jabadiagm/MSXgoauld_x/fpga/Goauld_x.srcs/sources_1/ip/ila_0_1/synth/ila_0.v

// (c) Copyright 1995-2012 Xilinx, Inc. All rights reserved.
//
// This file contains confidential and proprietary information
// of Xilinx, Inc. and is protected under U.S. and
// international copyright and other intellectual property
// laws.
//
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
// CRITICAL APPLICATIONS
// Xilinx products are not designed or intended to be fail-
// safe, or for use in any application requiring fail-safe
// performance, such as life-support or safety devices or
// systems, Class III medical devices, nuclear facilities,
// applications related to the deployment of airbags, or any
// other applications that could lead to death, personal
// injury, or severe property or environmental damage
// (individually and collectively, "Critical
// Applications"). Customer assumes the sole risk and
// liability of any use of Xilinx products in Critical
// Applications, subject only to applicable laws and
// regulations governing limitations on product liability.
//
// THIS COPYRIGHT NOTICE AND DISCLAIMER MUST BE RETAINED AS
// PART OF THIS FILE AT ALL TIMES.
//
// DO NOT MODIFY THIS FILE.
(* DowngradeIPIdentifiedWarnings="yes" *)
(* X_CORE_INFO = "ila,Vivado 2019.1" *)
(* CHECK_LICENSE_TYPE = "ila_0,ila,{}" *)
(* CORE_GENERATION_INFO = "ila_0,ila,{x_ipProduct=Vivado 2019.1,x_ipVendor=xilinx.com,x_ipLibrary=ip,x_ipName=ila,x_ipVersion=6.2,x_ipLanguage=VERILOG,C_XLNX_HW_PROBE_INFO=DEFAULT,C_XDEVICEFAMILY=artix7,C_CORE_TYPE=1,C_CORE_INFO1=0,C_CORE_INFO2=0,C_CAPTURE_TYPE=0,C_MU_TYPE=0,C_TC_TYPE=0,C_NUM_OF_PROBES=28,C_DATA_DEPTH=2048,C_MAJOR_VERSION=2019,C_MINOR_VERSION=1,C_BUILD_REVISION=0,C_CORE_MAJOR_VER=6,C_CORE_MINOR_VER=2,C_XSDB_SLAVE_TYPE=17,C_NEXT_SLAVE=0,C_CSE_DRV_VER=2,C_USE_TEST_REG=1,C_PIPE_IFACE=1,C_RAM_STYLE=SUBCORE,C_TRIGOUT_EN=0,C_TRIGIN_EN=0,C_ADV_TRIGGER=0,C_EN_DDR_ILA=0,C_DDR_CLK_GEN=0,C_CLK_FREQ=200,C_CLK_PERIOD=5.0,C_CLKFBOUT_MULT_F=10,C_DIVCLK_DIVIDE=3,C_CLKOUT0_DIVIDE_F=10,C_EN_STRG_QUAL=0,C_INPUT_PIPE_STAGES=0,ALL_PROBE_SAME_MU=TRUE,ALL_PROBE_SAME_MU_CNT=1,C_EN_TIME_TAG=0,C_TIME_TAG_WIDTH=32,C_ILA_CLK_FREQ=2000000,C_PROBE0_WIDTH=25,C_PROBE1_WIDTH=24,C_PROBE2_WIDTH=8,C_PROBE3_WIDTH=1,C_PROBE4_WIDTH=1,C_PROBE5_WIDTH=4,C_PROBE6_WIDTH=25,C_PROBE7_WIDTH=1,C_PROBE8_WIDTH=1,C_PROBE9_WIDTH=8,C_PROBE10_WIDTH=16,C_PROBE11_WIDTH=1,C_PROBE12_WIDTH=1,C_PROBE13_WIDTH=4,C_PROBE14_WIDTH=8,C_PROBE15_WIDTH=1,C_PROBE16_WIDTH=1,C_PROBE17_WIDTH=1,C_PROBE18_WIDTH=1,C_PROBE19_WIDTH=1,C_PROBE20_WIDTH=1,C_PROBE21_WIDTH=1,C_PROBE22_WIDTH=1,C_PROBE23_WIDTH=1,C_PROBE24_WIDTH=16,C_PROBE25_WIDTH=8,C_PROBE26_WIDTH=1,C_PROBE27_WIDTH=1,C_PROBE28_WIDTH=1,C_PROBE29_WIDTH=1,C_PROBE30_WIDTH=1,C_PROBE31_WIDTH=1,C_PROBE32_WIDTH=1,C_PROBE33_WIDTH=1,C_PROBE34_WIDTH=1,C_PROBE35_WIDTH=1,C_PROBE36_WIDTH=1,C_PROBE37_WIDTH=1,C_PROBE38_WIDTH=1,C_PROBE39_WIDTH=1,C_PROBE40_WIDTH=1,C_PROBE41_WIDTH=1,C_PROBE42_WIDTH=1,C_PROBE43_WIDTH=1,C_PROBE44_WIDTH=1,C_PROBE45_WIDTH=1,C_PROBE46_WIDTH=1,C_PROBE47_WIDTH=1,C_PROBE48_WIDTH=1,C_PROBE49_WIDTH=1,C_PROBE50_WIDTH=1,C_PROBE51_WIDTH=1,C_PROBE52_WIDTH=1,C_PROBE53_WIDTH=1,\
C_PROBE54_WIDTH=1,C_PROBE55_WIDTH=1,C_PROBE56_WIDTH=1,C_PROBE57_WIDTH=1,C_PROBE58_WIDTH=1,C_PROBE59_WIDTH=1,C_PROBE60_WIDTH=1,C_PROBE61_WIDTH=1,C_PROBE62_WIDTH=1,C_PROBE63_WIDTH=1,C_PROBE64_WIDTH=1,C_PROBE65_WIDTH=1,C_PROBE66_WIDTH=1,C_PROBE67_WIDTH=1,C_PROBE68_WIDTH=1,C_PROBE69_WIDTH=1,C_PROBE70_WIDTH=1,C_PROBE71_WIDTH=1,C_PROBE72_WIDTH=1,C_PROBE73_WIDTH=1,C_PROBE74_WIDTH=1,C_PROBE75_WIDTH=1,C_PROBE76_WIDTH=1,C_PROBE77_WIDTH=1,C_PROBE78_WIDTH=1,C_PROBE79_WIDTH=1,C_PROBE80_WIDTH=1,C_PROBE81_WIDTH=1,C_PROBE82_WIDTH=1,C_PROBE83_WIDTH=1,C_PROBE84_WIDTH=1,C_PROBE85_WIDTH=1,C_PROBE86_WIDTH=1,C_PROBE87_WIDTH=1,C_PROBE88_WIDTH=1,C_PROBE89_WIDTH=1,C_PROBE90_WIDTH=1,C_PROBE91_WIDTH=1,C_PROBE92_WIDTH=1,C_PROBE93_WIDTH=1,C_PROBE94_WIDTH=1,C_PROBE95_WIDTH=1,C_PROBE96_WIDTH=1,C_PROBE97_WIDTH=1,C_PROBE98_WIDTH=1,C_PROBE99_WIDTH=1,C_PROBE100_WIDTH=1,C_PROBE101_WIDTH=1,C_PROBE102_WIDTH=1,C_PROBE103_WIDTH=1,C_PROBE104_WIDTH=1,C_PROBE105_WIDTH=1,C_PROBE106_WIDTH=1,C_PROBE107_WIDTH=1,C_PROBE108_WIDTH=1,C_PROBE109_WIDTH=1,C_PROBE110_WIDTH=1,C_PROBE111_WIDTH=1,C_PROBE112_WIDTH=1,C_PROBE113_WIDTH=1,C_PROBE114_WIDTH=1,C_PROBE115_WIDTH=1,C_PROBE116_WIDTH=1,C_PROBE117_WIDTH=1,C_PROBE118_WIDTH=1,C_PROBE119_WIDTH=1,C_PROBE120_WIDTH=1,C_PROBE121_WIDTH=1,C_PROBE122_WIDTH=1,C_PROBE123_WIDTH=1,C_PROBE124_WIDTH=1,C_PROBE125_WIDTH=1,C_PROBE126_WIDTH=1,C_PROBE127_WIDTH=1,C_PROBE128_WIDTH=1,C_PROBE129_WIDTH=1,C_PROBE130_WIDTH=1,C_PROBE131_WIDTH=1,C_PROBE132_WIDTH=1,C_PROBE133_WIDTH=1,C_PROBE134_WIDTH=1,C_PROBE135_WIDTH=1,C_PROBE136_WIDTH=1,C_PROBE137_WIDTH=1,C_PROBE138_WIDTH=1,C_PROBE139_WIDTH=1,C_PROBE140_WIDTH=1,C_PROBE141_WIDTH=1,C_PROBE142_WIDTH=1,C_PROBE143_WIDTH=1,C_PROBE144_WIDTH=1,C_PROBE145_WIDTH=1,C_PROBE146_WIDTH=1,C_PROBE147_WIDTH=1,C_PROBE148_WIDTH=1,C_PROBE149_WIDTH=1,C_PROBE150_WIDTH=1,C_PROBE151_WIDTH=1,C_PROBE152_WIDTH=1,C_PROBE153_WIDTH=1,\
C_PROBE154_WIDTH=1,C_PROBE155_WIDTH=1,C_PROBE156_WIDTH=1,C_PROBE157_WIDTH=1,C_PROBE158_WIDTH=1,C_PROBE159_WIDTH=1,C_PROBE160_WIDTH=1,C_PROBE161_WIDTH=1,C_PROBE162_WIDTH=1,C_PROBE163_WIDTH=1,C_PROBE164_WIDTH=1,C_PROBE165_WIDTH=1,C_PROBE166_WIDTH=1,C_PROBE167_WIDTH=1,C_PROBE168_WIDTH=1,C_PROBE169_WIDTH=1,C_PROBE170_WIDTH=1,C_PROBE171_WIDTH=1,C_PROBE172_WIDTH=1,C_PROBE173_WIDTH=1,C_PROBE174_WIDTH=1,C_PROBE175_WIDTH=1,C_PROBE176_WIDTH=1,C_PROBE177_WIDTH=1,C_PROBE178_WIDTH=1,C_PROBE179_WIDTH=1,C_PROBE180_WIDTH=1,C_PROBE181_WIDTH=1,C_PROBE182_WIDTH=1,C_PROBE183_WIDTH=1,C_PROBE184_WIDTH=1,C_PROBE185_WIDTH=1,C_PROBE186_WIDTH=1,C_PROBE187_WIDTH=1,C_PROBE188_WIDTH=1,C_PROBE189_WIDTH=1,C_PROBE190_WIDTH=1,C_PROBE191_WIDTH=1,C_PROBE192_WIDTH=1,C_PROBE193_WIDTH=1,C_PROBE194_WIDTH=1,C_PROBE195_WIDTH=1,C_PROBE196_WIDTH=1,C_PROBE197_WIDTH=1,C_PROBE198_WIDTH=1,C_PROBE199_WIDTH=1,C_PROBE200_WIDTH=1,C_PROBE201_WIDTH=1,C_PROBE202_WIDTH=1,C_PROBE203_WIDTH=1,C_PROBE204_WIDTH=1,C_PROBE205_WIDTH=1,C_PROBE206_WIDTH=1,C_PROBE207_WIDTH=1,C_PROBE208_WIDTH=1,C_PROBE209_WIDTH=1,C_PROBE210_WIDTH=1,C_PROBE211_WIDTH=1,C_PROBE212_WIDTH=1,C_PROBE213_WIDTH=1,C_PROBE214_WIDTH=1,C_PROBE215_WIDTH=1,C_PROBE216_WIDTH=1,C_PROBE217_WIDTH=1,C_PROBE218_WIDTH=1,C_PROBE219_WIDTH=1,C_PROBE220_WIDTH=1,C_PROBE221_WIDTH=1,C_PROBE222_WIDTH=1,C_PROBE223_WIDTH=1,C_PROBE224_WIDTH=1,C_PROBE225_WIDTH=1,C_PROBE226_WIDTH=1,C_PROBE227_WIDTH=1,C_PROBE228_WIDTH=1,C_PROBE229_WIDTH=1,C_PROBE230_WIDTH=1,C_PROBE231_WIDTH=1,C_PROBE232_WIDTH=1,C_PROBE233_WIDTH=1,C_PROBE234_WIDTH=1,C_PROBE235_WIDTH=1,C_PROBE236_WIDTH=1,C_PROBE237_WIDTH=1,C_PROBE238_WIDTH=1,C_PROBE239_WIDTH=1,C_PROBE240_WIDTH=1,C_PROBE241_WIDTH=1,C_PROBE242_WIDTH=1,C_PROBE243_WIDTH=1,C_PROBE244_WIDTH=1,C_PROBE245_WIDTH=1,C_PROBE246_WIDTH=1,C_PROBE247_WIDTH=1,C_PROBE248_WIDTH=1,C_PROBE249_WIDTH=1,C_PROBE250_WIDTH=1,C_PROBE251_WIDTH=1,C_PROBE252_WIDTH=1,C_PROBE253_WIDTH=1,\
C_PROBE254_WIDTH=1,C_PROBE255_WIDTH=1,C_PROBE256_WIDTH=1,C_PROBE257_WIDTH=1,C_PROBE258_WIDTH=1,C_PROBE259_WIDTH=1,C_PROBE260_WIDTH=1,C_PROBE261_WIDTH=1,C_PROBE262_WIDTH=1,C_PROBE263_WIDTH=1,C_PROBE264_WIDTH=1,C_PROBE265_WIDTH=1,C_PROBE266_WIDTH=1,C_PROBE267_WIDTH=1,C_PROBE268_WIDTH=1,C_PROBE269_WIDTH=1,C_PROBE270_WIDTH=1,C_PROBE271_WIDTH=1,C_PROBE272_WIDTH=1,C_PROBE273_WIDTH=1,C_PROBE274_WIDTH=1,C_PROBE275_WIDTH=1,C_PROBE276_WIDTH=1,C_PROBE277_WIDTH=1,C_PROBE278_WIDTH=1,C_PROBE279_WIDTH=1,C_PROBE280_WIDTH=1,C_PROBE281_WIDTH=1,C_PROBE282_WIDTH=1,C_PROBE283_WIDTH=1,C_PROBE284_WIDTH=1,C_PROBE285_WIDTH=1,C_PROBE286_WIDTH=1,C_PROBE287_WIDTH=1,C_PROBE288_WIDTH=1,C_PROBE289_WIDTH=1,C_PROBE290_WIDTH=1,C_PROBE291_WIDTH=1,C_PROBE292_WIDTH=1,C_PROBE293_WIDTH=1,C_PROBE294_WIDTH=1,C_PROBE295_WIDTH=1,C_PROBE296_WIDTH=1,C_PROBE297_WIDTH=1,C_PROBE298_WIDTH=1,C_PROBE299_WIDTH=1,C_PROBE300_WIDTH=1,C_PROBE301_WIDTH=1,C_PROBE302_WIDTH=1,C_PROBE303_WIDTH=1,C_PROBE304_WIDTH=1,C_PROBE305_WIDTH=1,C_PROBE306_WIDTH=1,C_PROBE307_WIDTH=1,C_PROBE308_WIDTH=1,C_PROBE309_WIDTH=1,C_PROBE310_WIDTH=1,C_PROBE311_WIDTH=1,C_PROBE312_WIDTH=1,C_PROBE313_WIDTH=1,C_PROBE314_WIDTH=1,C_PROBE315_WIDTH=1,C_PROBE316_WIDTH=1,C_PROBE317_WIDTH=1,C_PROBE318_WIDTH=1,C_PROBE319_WIDTH=1,C_PROBE320_WIDTH=1,C_PROBE321_WIDTH=1,C_PROBE322_WIDTH=1,C_PROBE323_WIDTH=1,C_PROBE324_WIDTH=1,C_PROBE325_WIDTH=1,C_PROBE326_WIDTH=1,C_PROBE327_WIDTH=1,C_PROBE328_WIDTH=1,C_PROBE329_WIDTH=1,C_PROBE330_WIDTH=1,C_PROBE331_WIDTH=1,C_PROBE332_WIDTH=1,C_PROBE333_WIDTH=1,C_PROBE334_WIDTH=1,C_PROBE335_WIDTH=1,C_PROBE336_WIDTH=1,C_PROBE337_WIDTH=1,C_PROBE338_WIDTH=1,C_PROBE339_WIDTH=1,C_PROBE340_WIDTH=1,C_PROBE341_WIDTH=1,C_PROBE342_WIDTH=1,C_PROBE343_WIDTH=1,C_PROBE344_WIDTH=1,C_PROBE345_WIDTH=1,C_PROBE346_WIDTH=1,C_PROBE347_WIDTH=1,C_PROBE348_WIDTH=1,C_PROBE349_WIDTH=1,C_PROBE350_WIDTH=1,C_PROBE351_WIDTH=1,C_PROBE352_WIDTH=1,C_PROBE353_WIDTH=1,\
C_PROBE354_WIDTH=1,C_PROBE355_WIDTH=1,C_PROBE356_WIDTH=1,C_PROBE357_WIDTH=1,C_PROBE358_WIDTH=1,C_PROBE359_WIDTH=1,C_PROBE360_WIDTH=1,C_PROBE361_WIDTH=1,C_PROBE362_WIDTH=1,C_PROBE363_WIDTH=1,C_PROBE364_WIDTH=1,C_PROBE365_WIDTH=1,C_PROBE366_WIDTH=1,C_PROBE367_WIDTH=1,C_PROBE368_WIDTH=1,C_PROBE369_WIDTH=1,C_PROBE370_WIDTH=1,C_PROBE371_WIDTH=1,C_PROBE372_WIDTH=1,C_PROBE373_WIDTH=1,C_PROBE374_WIDTH=1,C_PROBE375_WIDTH=1,C_PROBE376_WIDTH=1,C_PROBE377_WIDTH=1,C_PROBE378_WIDTH=1,C_PROBE379_WIDTH=1,C_PROBE380_WIDTH=1,C_PROBE381_WIDTH=1,C_PROBE382_WIDTH=1,C_PROBE383_WIDTH=1,C_PROBE384_WIDTH=1,C_PROBE385_WIDTH=1,C_PROBE386_WIDTH=1,C_PROBE387_WIDTH=1,C_PROBE388_WIDTH=1,C_PROBE389_WIDTH=1,C_PROBE390_WIDTH=1,C_PROBE391_WIDTH=1,C_PROBE392_WIDTH=1,C_PROBE393_WIDTH=1,C_PROBE394_WIDTH=1,C_PROBE395_WIDTH=1,C_PROBE396_WIDTH=1,C_PROBE397_WIDTH=1,C_PROBE398_WIDTH=1,C_PROBE399_WIDTH=1,C_PROBE400_WIDTH=1,C_PROBE401_WIDTH=1,C_PROBE402_WIDTH=1,C_PROBE403_WIDTH=1,C_PROBE404_WIDTH=1,C_PROBE405_WIDTH=1,C_PROBE406_WIDTH=1,C_PROBE407_WIDTH=1,C_PROBE408_WIDTH=1,C_PROBE409_WIDTH=1,C_PROBE410_WIDTH=1,C_PROBE411_WIDTH=1,C_PROBE412_WIDTH=1,C_PROBE413_WIDTH=1,C_PROBE414_WIDTH=1,C_PROBE415_WIDTH=1,C_PROBE416_WIDTH=1,C_PROBE417_WIDTH=1,C_PROBE418_WIDTH=1,C_PROBE419_WIDTH=1,C_PROBE420_WIDTH=1,C_PROBE421_WIDTH=1,C_PROBE422_WIDTH=1,C_PROBE423_WIDTH=1,C_PROBE424_WIDTH=1,C_PROBE425_WIDTH=1,C_PROBE426_WIDTH=1,C_PROBE427_WIDTH=1,C_PROBE428_WIDTH=1,C_PROBE429_WIDTH=1,C_PROBE430_WIDTH=1,C_PROBE431_WIDTH=1,C_PROBE432_WIDTH=1,C_PROBE433_WIDTH=1,C_PROBE434_WIDTH=1,C_PROBE435_WIDTH=1,C_PROBE436_WIDTH=1,C_PROBE437_WIDTH=1,C_PROBE438_WIDTH=1,C_PROBE439_WIDTH=1,C_PROBE440_WIDTH=1,C_PROBE441_WIDTH=1,C_PROBE442_WIDTH=1,C_PROBE443_WIDTH=1,C_PROBE444_WIDTH=1,C_PROBE445_WIDTH=1,C_PROBE446_WIDTH=1,C_PROBE447_WIDTH=1,C_PROBE448_WIDTH=1,C_PROBE449_WIDTH=1,C_PROBE450_WIDTH=1,C_PROBE451_WIDTH=1,C_PROBE452_WIDTH=1,C_PROBE453_WIDTH=1,\
C_PROBE454_WIDTH=1,C_PROBE455_WIDTH=1,C_PROBE456_WIDTH=1,C_PROBE457_WIDTH=1,C_PROBE458_WIDTH=1,C_PROBE459_WIDTH=1,C_PROBE460_WIDTH=1,C_PROBE461_WIDTH=1,C_PROBE462_WIDTH=1,C_PROBE463_WIDTH=1,C_PROBE464_WIDTH=1,C_PROBE465_WIDTH=1,C_PROBE466_WIDTH=1,C_PROBE467_WIDTH=1,C_PROBE468_WIDTH=1,C_PROBE469_WIDTH=1,C_PROBE470_WIDTH=1,C_PROBE471_WIDTH=1,C_PROBE472_WIDTH=1,C_PROBE473_WIDTH=1,C_PROBE474_WIDTH=1,C_PROBE475_WIDTH=1,C_PROBE476_WIDTH=1,C_PROBE477_WIDTH=1,C_PROBE478_WIDTH=1,C_PROBE479_WIDTH=1,C_PROBE480_WIDTH=1,C_PROBE481_WIDTH=1,C_PROBE482_WIDTH=1,C_PROBE483_WIDTH=1,C_PROBE484_WIDTH=1,C_PROBE485_WIDTH=1,C_PROBE486_WIDTH=1,C_PROBE487_WIDTH=1,C_PROBE488_WIDTH=1,C_PROBE489_WIDTH=1,C_PROBE490_WIDTH=1,C_PROBE491_WIDTH=1,C_PROBE492_WIDTH=1,C_PROBE493_WIDTH=1,C_PROBE494_WIDTH=1,C_PROBE495_WIDTH=1,C_PROBE496_WIDTH=1,C_PROBE497_WIDTH=1,C_PROBE498_WIDTH=1,C_PROBE499_WIDTH=1,C_PROBE500_WIDTH=1,C_PROBE501_WIDTH=1,C_PROBE502_WIDTH=1,C_PROBE503_WIDTH=1,C_PROBE504_WIDTH=1,C_PROBE505_WIDTH=1,C_PROBE506_WIDTH=1,C_PROBE507_WIDTH=1,C_PROBE508_WIDTH=1,C_PROBE509_WIDTH=1,C_PROBE510_WIDTH=1,C_PROBE511_WIDTH=1,C_PROBE512_WIDTH=1,C_PROBE513_WIDTH=1,C_PROBE514_WIDTH=1,C_PROBE515_WIDTH=1,C_PROBE516_WIDTH=1,C_PROBE517_WIDTH=1,C_PROBE518_WIDTH=1,C_PROBE519_WIDTH=1,C_PROBE520_WIDTH=1,C_PROBE521_WIDTH=1,C_PROBE522_WIDTH=1,C_PROBE523_WIDTH=1,C_PROBE524_WIDTH=1,C_PROBE525_WIDTH=1,C_PROBE526_WIDTH=1,C_PROBE527_WIDTH=1,C_PROBE528_WIDTH=1,C_PROBE529_WIDTH=1,C_PROBE530_WIDTH=1,C_PROBE531_WIDTH=1,C_PROBE532_WIDTH=1,C_PROBE533_WIDTH=1,C_PROBE534_WIDTH=1,C_PROBE535_WIDTH=1,C_PROBE536_WIDTH=1,C_PROBE537_WIDTH=1,C_PROBE538_WIDTH=1,C_PROBE539_WIDTH=1,C_PROBE540_WIDTH=1,C_PROBE541_WIDTH=1,C_PROBE542_WIDTH=1,C_PROBE543_WIDTH=1,C_PROBE544_WIDTH=1,C_PROBE545_WIDTH=1,C_PROBE546_WIDTH=1,C_PROBE547_WIDTH=1,C_PROBE548_WIDTH=1,C_PROBE549_WIDTH=1,C_PROBE550_WIDTH=1,C_PROBE551_WIDTH=1,C_PROBE552_WIDTH=1,C_PROBE553_WIDTH=1,\
C_PROBE554_WIDTH=1,C_PROBE555_WIDTH=1,C_PROBE556_WIDTH=1,C_PROBE557_WIDTH=1,C_PROBE558_WIDTH=1,C_PROBE559_WIDTH=1,C_PROBE560_WIDTH=1,C_PROBE561_WIDTH=1,C_PROBE562_WIDTH=1,C_PROBE563_WIDTH=1,C_PROBE564_WIDTH=1,C_PROBE565_WIDTH=1,C_PROBE566_WIDTH=1,C_PROBE567_WIDTH=1,C_PROBE568_WIDTH=1,C_PROBE569_WIDTH=1,C_PROBE570_WIDTH=1,C_PROBE571_WIDTH=1,C_PROBE572_WIDTH=1,C_PROBE573_WIDTH=1,C_PROBE574_WIDTH=1,C_PROBE575_WIDTH=1,C_PROBE576_WIDTH=1,C_PROBE577_WIDTH=1,C_PROBE578_WIDTH=1,C_PROBE579_WIDTH=1,C_PROBE580_WIDTH=1,C_PROBE581_WIDTH=1,C_PROBE582_WIDTH=1,C_PROBE583_WIDTH=1,C_PROBE584_WIDTH=1,C_PROBE585_WIDTH=1,C_PROBE586_WIDTH=1,C_PROBE587_WIDTH=1,C_PROBE588_WIDTH=1,C_PROBE589_WIDTH=1,C_PROBE590_WIDTH=1,C_PROBE591_WIDTH=1,C_PROBE592_WIDTH=1,C_PROBE593_WIDTH=1,C_PROBE594_WIDTH=1,C_PROBE595_WIDTH=1,C_PROBE596_WIDTH=1,C_PROBE597_WIDTH=1,C_PROBE598_WIDTH=1,C_PROBE599_WIDTH=1,C_PROBE600_WIDTH=1,C_PROBE601_WIDTH=1,C_PROBE602_WIDTH=1,C_PROBE603_WIDTH=1,C_PROBE604_WIDTH=1,C_PROBE605_WIDTH=1,C_PROBE606_WIDTH=1,C_PROBE607_WIDTH=1,C_PROBE608_WIDTH=1,C_PROBE609_WIDTH=1,C_PROBE610_WIDTH=1,C_PROBE611_WIDTH=1,C_PROBE612_WIDTH=1,C_PROBE613_WIDTH=1,C_PROBE614_WIDTH=1,C_PROBE615_WIDTH=1,C_PROBE616_WIDTH=1,C_PROBE617_WIDTH=1,C_PROBE618_WIDTH=1,C_PROBE619_WIDTH=1,C_PROBE620_WIDTH=1,C_PROBE621_WIDTH=1,C_PROBE622_WIDTH=1,C_PROBE623_WIDTH=1,C_PROBE624_WIDTH=1,C_PROBE625_WIDTH=1,C_PROBE626_WIDTH=1,C_PROBE627_WIDTH=1,C_PROBE628_WIDTH=1,C_PROBE629_WIDTH=1,C_PROBE630_WIDTH=1,C_PROBE631_WIDTH=1,C_PROBE632_WIDTH=1,C_PROBE633_WIDTH=1,C_PROBE634_WIDTH=1,C_PROBE635_WIDTH=1,C_PROBE636_WIDTH=1,C_PROBE637_WIDTH=1,C_PROBE638_WIDTH=1,C_PROBE639_WIDTH=1,C_PROBE640_WIDTH=1,C_PROBE641_WIDTH=1,C_PROBE642_WIDTH=1,C_PROBE643_WIDTH=1,C_PROBE644_WIDTH=1,C_PROBE645_WIDTH=1,C_PROBE646_WIDTH=1,C_PROBE647_WIDTH=1,C_PROBE648_WIDTH=1,C_PROBE649_WIDTH=1,C_PROBE650_WIDTH=1,C_PROBE651_WIDTH=1,C_PROBE652_WIDTH=1,C_PROBE653_WIDTH=1,\
C_PROBE654_WIDTH=1,C_PROBE655_WIDTH=1,C_PROBE656_WIDTH=1,C_PROBE657_WIDTH=1,C_PROBE658_WIDTH=1,C_PROBE659_WIDTH=1,C_PROBE660_WIDTH=1,C_PROBE661_WIDTH=1,C_PROBE662_WIDTH=1,C_PROBE663_WIDTH=1,C_PROBE664_WIDTH=1,C_PROBE665_WIDTH=1,C_PROBE666_WIDTH=1,C_PROBE667_WIDTH=1,C_PROBE668_WIDTH=1,C_PROBE669_WIDTH=1,C_PROBE670_WIDTH=1,C_PROBE671_WIDTH=1,C_PROBE672_WIDTH=1,C_PROBE673_WIDTH=1,C_PROBE674_WIDTH=1,C_PROBE675_WIDTH=1,C_PROBE676_WIDTH=1,C_PROBE677_WIDTH=1,C_PROBE678_WIDTH=1,C_PROBE679_WIDTH=1,C_PROBE680_WIDTH=1,C_PROBE681_WIDTH=1,C_PROBE682_WIDTH=1,C_PROBE683_WIDTH=1,C_PROBE684_WIDTH=1,C_PROBE685_WIDTH=1,C_PROBE686_WIDTH=1,C_PROBE687_WIDTH=1,C_PROBE688_WIDTH=1,C_PROBE689_WIDTH=1,C_PROBE690_WIDTH=1,C_PROBE691_WIDTH=1,C_PROBE692_WIDTH=1,C_PROBE693_WIDTH=1,C_PROBE694_WIDTH=1,C_PROBE695_WIDTH=1,C_PROBE696_WIDTH=1,C_PROBE697_WIDTH=1,C_PROBE698_WIDTH=1,C_PROBE699_WIDTH=1,C_PROBE700_WIDTH=1,C_PROBE701_WIDTH=1,C_PROBE702_WIDTH=1,C_PROBE703_WIDTH=1,C_PROBE704_WIDTH=1,C_PROBE705_WIDTH=1,C_PROBE706_WIDTH=1,C_PROBE707_WIDTH=1,C_PROBE708_WIDTH=1,C_PROBE709_WIDTH=1,C_PROBE710_WIDTH=1,C_PROBE711_WIDTH=1,C_PROBE712_WIDTH=1,C_PROBE713_WIDTH=1,C_PROBE714_WIDTH=1,C_PROBE715_WIDTH=1,C_PROBE716_WIDTH=1,C_PROBE717_WIDTH=1,C_PROBE718_WIDTH=1,C_PROBE719_WIDTH=1,C_PROBE720_WIDTH=1,C_PROBE721_WIDTH=1,C_PROBE722_WIDTH=1,C_PROBE723_WIDTH=1,C_PROBE724_WIDTH=1,C_PROBE725_WIDTH=1,C_PROBE726_WIDTH=1,C_PROBE727_WIDTH=1,C_PROBE728_WIDTH=1,C_PROBE729_WIDTH=1,C_PROBE730_WIDTH=1,C_PROBE731_WIDTH=1,C_PROBE732_WIDTH=1,C_PROBE733_WIDTH=1,C_PROBE734_WIDTH=1,C_PROBE735_WIDTH=1,C_PROBE736_WIDTH=1,C_PROBE737_WIDTH=1,C_PROBE738_WIDTH=1,C_PROBE739_WIDTH=1,C_PROBE740_WIDTH=1,C_PROBE741_WIDTH=1,C_PROBE742_WIDTH=1,C_PROBE743_WIDTH=1,C_PROBE744_WIDTH=1,C_PROBE745_WIDTH=1,C_PROBE746_WIDTH=1,C_PROBE747_WIDTH=1,C_PROBE748_WIDTH=1,C_PROBE749_WIDTH=1,C_PROBE750_WIDTH=1,C_PROBE751_WIDTH=1,C_PROBE752_WIDTH=1,C_PROBE753_WIDTH=1,\
C_PROBE754_WIDTH=1,C_PROBE755_WIDTH=1,C_PROBE756_WIDTH=1,C_PROBE757_WIDTH=1,C_PROBE758_WIDTH=1,C_PROBE759_WIDTH=1,C_PROBE760_WIDTH=1,C_PROBE761_WIDTH=1,C_PROBE762_WIDTH=1,C_PROBE763_WIDTH=1,C_PROBE764_WIDTH=1,C_PROBE765_WIDTH=1,C_PROBE766_WIDTH=1,C_PROBE767_WIDTH=1,C_PROBE768_WIDTH=1,C_PROBE769_WIDTH=1,C_PROBE770_WIDTH=1,C_PROBE771_WIDTH=1,C_PROBE772_WIDTH=1,C_PROBE773_WIDTH=1,C_PROBE774_WIDTH=1,C_PROBE775_WIDTH=1,C_PROBE776_WIDTH=1,C_PROBE777_WIDTH=1,C_PROBE778_WIDTH=1,C_PROBE779_WIDTH=1,C_PROBE780_WIDTH=1,C_PROBE781_WIDTH=1,C_PROBE782_WIDTH=1,C_PROBE783_WIDTH=1,C_PROBE784_WIDTH=1,C_PROBE785_WIDTH=1,C_PROBE786_WIDTH=1,C_PROBE787_WIDTH=1,C_PROBE788_WIDTH=1,C_PROBE789_WIDTH=1,C_PROBE790_WIDTH=1,C_PROBE791_WIDTH=1,C_PROBE792_WIDTH=1,C_PROBE793_WIDTH=1,C_PROBE794_WIDTH=1,C_PROBE795_WIDTH=1,C_PROBE796_WIDTH=1,C_PROBE797_WIDTH=1,C_PROBE798_WIDTH=1,C_PROBE799_WIDTH=1,C_PROBE800_WIDTH=1,C_PROBE801_WIDTH=1,C_PROBE802_WIDTH=1,C_PROBE803_WIDTH=1,C_PROBE804_WIDTH=1,C_PROBE805_WIDTH=1,C_PROBE806_WIDTH=1,C_PROBE807_WIDTH=1,C_PROBE808_WIDTH=1,C_PROBE809_WIDTH=1,C_PROBE810_WIDTH=1,C_PROBE811_WIDTH=1,C_PROBE812_WIDTH=1,C_PROBE813_WIDTH=1,C_PROBE814_WIDTH=1,C_PROBE815_WIDTH=1,C_PROBE816_WIDTH=1,C_PROBE817_WIDTH=1,C_PROBE818_WIDTH=1,C_PROBE819_WIDTH=1,C_PROBE820_WIDTH=1,C_PROBE821_WIDTH=1,C_PROBE822_WIDTH=1,C_PROBE823_WIDTH=1,C_PROBE824_WIDTH=1,C_PROBE825_WIDTH=1,C_PROBE826_WIDTH=1,C_PROBE827_WIDTH=1,C_PROBE828_WIDTH=1,C_PROBE829_WIDTH=1,C_PROBE830_WIDTH=1,C_PROBE831_WIDTH=1,C_PROBE832_WIDTH=1,C_PROBE833_WIDTH=1,C_PROBE834_WIDTH=1,C_PROBE835_WIDTH=1,C_PROBE836_WIDTH=1,C_PROBE837_WIDTH=1,C_PROBE838_WIDTH=1,C_PROBE839_WIDTH=1,C_PROBE840_WIDTH=1,C_PROBE841_WIDTH=1,C_PROBE842_WIDTH=1,C_PROBE843_WIDTH=1,C_PROBE844_WIDTH=1,C_PROBE845_WIDTH=1,C_PROBE846_WIDTH=1,C_PROBE847_WIDTH=1,C_PROBE848_WIDTH=1,C_PROBE849_WIDTH=1,C_PROBE850_WIDTH=1,C_PROBE851_WIDTH=1,C_PROBE852_WIDTH=1,C_PROBE853_WIDTH=1,\
C_PROBE854_WIDTH=1,C_PROBE855_WIDTH=1,C_PROBE856_WIDTH=1,C_PROBE857_WIDTH=1,C_PROBE858_WIDTH=1,C_PROBE859_WIDTH=1,C_PROBE860_WIDTH=1,C_PROBE861_WIDTH=1,C_PROBE862_WIDTH=1,C_PROBE863_WIDTH=1,C_PROBE864_WIDTH=1,C_PROBE865_WIDTH=1,C_PROBE866_WIDTH=1,C_PROBE867_WIDTH=1,C_PROBE868_WIDTH=1,C_PROBE869_WIDTH=1,C_PROBE870_WIDTH=1,C_PROBE871_WIDTH=1,C_PROBE872_WIDTH=1,C_PROBE873_WIDTH=1,C_PROBE874_WIDTH=1,C_PROBE875_WIDTH=1,C_PROBE876_WIDTH=1,C_PROBE877_WIDTH=1,C_PROBE878_WIDTH=1,C_PROBE879_WIDTH=1,C_PROBE880_WIDTH=1,C_PROBE881_WIDTH=1,C_PROBE882_WIDTH=1,C_PROBE883_WIDTH=1,C_PROBE884_WIDTH=1,C_PROBE885_WIDTH=1,C_PROBE886_WIDTH=1,C_PROBE887_WIDTH=1,C_PROBE888_WIDTH=1,C_PROBE889_WIDTH=1,C_PROBE890_WIDTH=1,C_PROBE891_WIDTH=1,C_PROBE892_WIDTH=1,C_PROBE893_WIDTH=1,C_PROBE894_WIDTH=1,C_PROBE895_WIDTH=1,C_PROBE896_WIDTH=1,C_PROBE897_WIDTH=1,C_PROBE898_WIDTH=1,C_PROBE899_WIDTH=1,C_PROBE900_WIDTH=1,C_PROBE901_WIDTH=1,C_PROBE902_WIDTH=1,C_PROBE903_WIDTH=1,C_PROBE904_WIDTH=1,C_PROBE905_WIDTH=1,C_PROBE906_WIDTH=1,C_PROBE907_WIDTH=1,C_PROBE908_WIDTH=1,C_PROBE909_WIDTH=1,C_PROBE910_WIDTH=1,C_PROBE911_WIDTH=1,C_PROBE912_WIDTH=1,C_PROBE913_WIDTH=1,C_PROBE914_WIDTH=1,C_PROBE915_WIDTH=1,C_PROBE916_WIDTH=1,C_PROBE917_WIDTH=1,C_PROBE918_WIDTH=1,C_PROBE919_WIDTH=1,C_PROBE920_WIDTH=1,C_PROBE921_WIDTH=1,C_PROBE922_WIDTH=1,C_PROBE923_WIDTH=1,C_PROBE924_WIDTH=1,C_PROBE925_WIDTH=1,C_PROBE926_WIDTH=1,C_PROBE927_WIDTH=1,C_PROBE928_WIDTH=1,C_PROBE929_WIDTH=1,C_PROBE930_WIDTH=1,C_PROBE931_WIDTH=1,C_PROBE932_WIDTH=1,C_PROBE933_WIDTH=1,C_PROBE934_WIDTH=1,C_PROBE935_WIDTH=1,C_PROBE936_WIDTH=1,C_PROBE937_WIDTH=1,C_PROBE938_WIDTH=1,C_PROBE939_WIDTH=1,C_PROBE940_WIDTH=1,C_PROBE941_WIDTH=1,C_PROBE942_WIDTH=1,C_PROBE943_WIDTH=1,C_PROBE944_WIDTH=1,C_PROBE945_WIDTH=1,C_PROBE946_WIDTH=1,C_PROBE947_WIDTH=1,C_PROBE948_WIDTH=1,C_PROBE949_WIDTH=1,C_PROBE950_WIDTH=1,C_PROBE951_WIDTH=1,C_PROBE952_WIDTH=1,C_PROBE953_WIDTH=1,\
C_PROBE954_WIDTH=1,C_PROBE955_WIDTH=1,C_PROBE956_WIDTH=1,C_PROBE957_WIDTH=1,C_PROBE958_WIDTH=1,C_PROBE959_WIDTH=1,C_PROBE960_WIDTH=1,C_PROBE961_WIDTH=1,C_PROBE962_WIDTH=1,C_PROBE963_WIDTH=1,C_PROBE964_WIDTH=1,C_PROBE965_WIDTH=1,C_PROBE966_WIDTH=1,C_PROBE967_WIDTH=1,C_PROBE968_WIDTH=1,C_PROBE969_WIDTH=1,C_PROBE970_WIDTH=1,C_PROBE971_WIDTH=1,C_PROBE972_WIDTH=1,C_PROBE973_WIDTH=1,C_PROBE974_WIDTH=1,C_PROBE975_WIDTH=1,C_PROBE976_WIDTH=1,C_PROBE977_WIDTH=1,C_PROBE978_WIDTH=1,C_PROBE979_WIDTH=1,C_PROBE980_WIDTH=1,C_PROBE981_WIDTH=1,C_PROBE982_WIDTH=1,C_PROBE983_WIDTH=1,C_PROBE984_WIDTH=1,C_PROBE985_WIDTH=1,C_PROBE986_WIDTH=1,C_PROBE987_WIDTH=1,C_PROBE988_WIDTH=1,C_PROBE989_WIDTH=1,C_PROBE990_WIDTH=1,C_PROBE991_WIDTH=1,C_PROBE992_WIDTH=1,C_PROBE993_WIDTH=1,C_PROBE994_WIDTH=1,C_PROBE995_WIDTH=1,C_PROBE996_WIDTH=1,C_PROBE997_WIDTH=1,C_PROBE998_WIDTH=1,C_PROBE999_WIDTH=1,C_PROBE1000_WIDTH=1,C_PROBE1001_WIDTH=1,C_PROBE1002_WIDTH=1,C_PROBE1003_WIDTH=1,C_PROBE1004_WIDTH=1,C_PROBE1005_WIDTH=1,C_PROBE1006_WIDTH=1,C_PROBE1007_WIDTH=1,C_PROBE1008_WIDTH=1,C_PROBE1009_WIDTH=1,C_PROBE1010_WIDTH=1,C_PROBE1011_WIDTH=1,C_PROBE1012_WIDTH=1,C_PROBE1013_WIDTH=1,C_PROBE1014_WIDTH=1,C_PROBE1015_WIDTH=1,C_PROBE1016_WIDTH=1,C_PROBE1017_WIDTH=1,C_PROBE1018_WIDTH=1,C_PROBE1019_WIDTH=1,C_PROBE1020_WIDTH=1,C_PROBE1021_WIDTH=1,C_PROBE1022_WIDTH=1,C_PROBE1023_WIDTH=1,C_PROBE0_MU_CNT=1,C_PROBE1_MU_CNT=1,C_PROBE2_MU_CNT=1,C_PROBE3_MU_CNT=1,C_PROBE4_MU_CNT=1,C_PROBE5_MU_CNT=1,C_PROBE6_MU_CNT=1,C_PROBE7_MU_CNT=1,C_PROBE8_MU_CNT=1,C_PROBE9_MU_CNT=1,C_PROBE10_MU_CNT=1,C_PROBE11_MU_CNT=1,C_PROBE12_MU_CNT=1,C_PROBE13_MU_CNT=1,C_PROBE14_MU_CNT=1,C_PROBE15_MU_CNT=1,C_PROBE16_MU_CNT=1,C_PROBE17_MU_CNT=1,C_PROBE18_MU_CNT=1,C_PROBE19_MU_CNT=1,C_PROBE20_MU_CNT=1,C_PROBE21_MU_CNT=1,C_PROBE22_MU_CNT=1,C_PROBE23_MU_CNT=1,C_PROBE24_MU_CNT=1,C_PROBE25_MU_CNT=1,C_PROBE26_MU_CNT=1,C_PROBE27_MU_CNT=1,C_PROBE28_MU_CNT=1,C_PROBE29_MU_CNT=1,\
C_PROBE30_MU_CNT=1,C_PROBE31_MU_CNT=1,C_PROBE32_MU_CNT=1,C_PROBE33_MU_CNT=1,C_PROBE34_MU_CNT=1,C_PROBE35_MU_CNT=1,C_PROBE36_MU_CNT=1,C_PROBE37_MU_CNT=1,C_PROBE38_MU_CNT=1,C_PROBE39_MU_CNT=1,C_PROBE40_MU_CNT=1,C_PROBE41_MU_CNT=1,C_PROBE42_MU_CNT=1,C_PROBE43_MU_CNT=1,C_PROBE44_MU_CNT=1,C_PROBE45_MU_CNT=1,C_PROBE46_MU_CNT=1,C_PROBE47_MU_CNT=1,C_PROBE48_MU_CNT=1,C_PROBE49_MU_CNT=1,C_PROBE50_MU_CNT=1,C_PROBE51_MU_CNT=1,C_PROBE52_MU_CNT=1,C_PROBE53_MU_CNT=1,C_PROBE54_MU_CNT=1,C_PROBE55_MU_CNT=1,C_PROBE56_MU_CNT=1,C_PROBE57_MU_CNT=1,C_PROBE58_MU_CNT=1,C_PROBE59_MU_CNT=1,C_PROBE60_MU_CNT=1,C_PROBE61_MU_CNT=1,C_PROBE62_MU_CNT=1,C_PROBE63_MU_CNT=1,C_PROBE64_MU_CNT=1,C_PROBE65_MU_CNT=1,C_PROBE66_MU_CNT=1,C_PROBE67_MU_CNT=1,C_PROBE68_MU_CNT=1,C_PROBE69_MU_CNT=1,C_PROBE70_MU_CNT=1,C_PROBE71_MU_CNT=1,C_PROBE72_MU_CNT=1,C_PROBE73_MU_CNT=1,C_PROBE74_MU_CNT=1,C_PROBE75_MU_CNT=1,C_PROBE76_MU_CNT=1,C_PROBE77_MU_CNT=1,C_PROBE78_MU_CNT=1,C_PROBE79_MU_CNT=1,C_PROBE80_MU_CNT=1,C_PROBE81_MU_CNT=1,C_PROBE82_MU_CNT=1,C_PROBE83_MU_CNT=1,C_PROBE84_MU_CNT=1,C_PROBE85_MU_CNT=1,C_PROBE86_MU_CNT=1,C_PROBE87_MU_CNT=1,C_PROBE88_MU_CNT=1,C_PROBE89_MU_CNT=1,C_PROBE90_MU_CNT=1,C_PROBE91_MU_CNT=1,C_PROBE92_MU_CNT=1,C_PROBE93_MU_CNT=1,C_PROBE94_MU_CNT=1,C_PROBE95_MU_CNT=1,C_PROBE96_MU_CNT=1,C_PROBE97_MU_CNT=1,C_PROBE98_MU_CNT=1,C_PROBE99_MU_CNT=1,C_PROBE100_MU_CNT=1,C_PROBE101_MU_CNT=1,C_PROBE102_MU_CNT=1,C_PROBE103_MU_CNT=1,C_PROBE104_MU_CNT=1,C_PROBE105_MU_CNT=1,C_PROBE106_MU_CNT=1,C_PROBE107_MU_CNT=1,C_PROBE108_MU_CNT=1,C_PROBE109_MU_CNT=1,C_PROBE110_MU_CNT=1,C_PROBE111_MU_CNT=1,C_PROBE112_MU_CNT=1,C_PROBE113_MU_CNT=1,C_PROBE114_MU_CNT=1,C_PROBE115_MU_CNT=1,C_PROBE116_MU_CNT=1,C_PROBE117_MU_CNT=1,C_PROBE118_MU_CNT=1,C_PROBE119_MU_CNT=1,C_PROBE120_MU_CNT=1,C_PROBE121_MU_CNT=1,C_PROBE122_MU_CNT=1,C_PROBE123_MU_CNT=1,C_PROBE124_MU_CNT=1,C_PROBE125_MU_CNT=1,C_PROBE126_MU_CNT=1,C_PROBE127_MU_CNT=1,C_PROBE128_MU_CNT=1,C_PROBE129_MU_CNT=1,\
C_PROBE130_MU_CNT=1,C_PROBE131_MU_CNT=1,C_PROBE132_MU_CNT=1,C_PROBE133_MU_CNT=1,C_PROBE134_MU_CNT=1,C_PROBE135_MU_CNT=1,C_PROBE136_MU_CNT=1,C_PROBE137_MU_CNT=1,C_PROBE138_MU_CNT=1,C_PROBE139_MU_CNT=1,C_PROBE140_MU_CNT=1,C_PROBE141_MU_CNT=1,C_PROBE142_MU_CNT=1,C_PROBE143_MU_CNT=1,C_PROBE144_MU_CNT=1,C_PROBE145_MU_CNT=1,C_PROBE146_MU_CNT=1,C_PROBE147_MU_CNT=1,C_PROBE148_MU_CNT=1,C_PROBE149_MU_CNT=1,C_PROBE150_MU_CNT=1,C_PROBE151_MU_CNT=1,C_PROBE152_MU_CNT=1,C_PROBE153_MU_CNT=1,C_PROBE154_MU_CNT=1,C_PROBE155_MU_CNT=1,C_PROBE156_MU_CNT=1,C_PROBE157_MU_CNT=1,C_PROBE158_MU_CNT=1,C_PROBE159_MU_CNT=1,C_PROBE160_MU_CNT=1,C_PROBE161_MU_CNT=1,C_PROBE162_MU_CNT=1,C_PROBE163_MU_CNT=1,C_PROBE164_MU_CNT=1,C_PROBE165_MU_CNT=1,C_PROBE166_MU_CNT=1,C_PROBE167_MU_CNT=1,C_PROBE168_MU_CNT=1,C_PROBE169_MU_CNT=1,C_PROBE170_MU_CNT=1,C_PROBE171_MU_CNT=1,C_PROBE172_MU_CNT=1,C_PROBE173_MU_CNT=1,C_PROBE174_MU_CNT=1,C_PROBE175_MU_CNT=1,C_PROBE176_MU_CNT=1,C_PROBE177_MU_CNT=1,C_PROBE178_MU_CNT=1,C_PROBE179_MU_CNT=1,C_PROBE180_MU_CNT=1,C_PROBE181_MU_CNT=1,C_PROBE182_MU_CNT=1,C_PROBE183_MU_CNT=1,C_PROBE184_MU_CNT=1,C_PROBE185_MU_CNT=1,C_PROBE186_MU_CNT=1,C_PROBE187_MU_CNT=1,C_PROBE188_MU_CNT=1,C_PROBE189_MU_CNT=1,C_PROBE190_MU_CNT=1,C_PROBE191_MU_CNT=1,C_PROBE192_MU_CNT=1,C_PROBE193_MU_CNT=1,C_PROBE194_MU_CNT=1,C_PROBE195_MU_CNT=1,C_PROBE196_MU_CNT=1,C_PROBE197_MU_CNT=1,C_PROBE198_MU_CNT=1,C_PROBE199_MU_CNT=1,C_PROBE200_MU_CNT=1,C_PROBE201_MU_CNT=1,C_PROBE202_MU_CNT=1,C_PROBE203_MU_CNT=1,C_PROBE204_MU_CNT=1,C_PROBE205_MU_CNT=1,C_PROBE206_MU_CNT=1,C_PROBE207_MU_CNT=1,C_PROBE208_MU_CNT=1,C_PROBE209_MU_CNT=1,C_PROBE210_MU_CNT=1,C_PROBE211_MU_CNT=1,C_PROBE212_MU_CNT=1,C_PROBE213_MU_CNT=1,C_PROBE214_MU_CNT=1,C_PROBE215_MU_CNT=1,C_PROBE216_MU_CNT=1,C_PROBE217_MU_CNT=1,C_PROBE218_MU_CNT=1,C_PROBE219_MU_CNT=1,C_PROBE220_MU_CNT=1,C_PROBE221_MU_CNT=1,C_PROBE222_MU_CNT=1,C_PROBE223_MU_CNT=1,C_PROBE224_MU_CNT=1,C_PROBE225_MU_CNT=1,C_PROBE226_MU_CNT=1,C_PROBE227_MU_CNT=1,C_PROBE228_MU_CNT=1,C_PROBE229_MU_CNT=1,\
C_PROBE230_MU_CNT=1,C_PROBE231_MU_CNT=1,C_PROBE232_MU_CNT=1,C_PROBE233_MU_CNT=1,C_PROBE234_MU_CNT=1,C_PROBE235_MU_CNT=1,C_PROBE236_MU_CNT=1,C_PROBE237_MU_CNT=1,C_PROBE238_MU_CNT=1,C_PROBE239_MU_CNT=1,C_PROBE240_MU_CNT=1,C_PROBE241_MU_CNT=1,C_PROBE242_MU_CNT=1,C_PROBE243_MU_CNT=1,C_PROBE244_MU_CNT=1,C_PROBE245_MU_CNT=1,C_PROBE246_MU_CNT=1,C_PROBE247_MU_CNT=1,C_PROBE248_MU_CNT=1,C_PROBE249_MU_CNT=1,C_PROBE250_MU_CNT=1,C_PROBE251_MU_CNT=1,C_PROBE252_MU_CNT=1,C_PROBE253_MU_CNT=1,C_PROBE254_MU_CNT=1,C_PROBE255_MU_CNT=1,C_PROBE256_MU_CNT=1,C_PROBE257_MU_CNT=1,C_PROBE258_MU_CNT=1,C_PROBE259_MU_CNT=1,C_PROBE260_MU_CNT=1,C_PROBE261_MU_CNT=1,C_PROBE262_MU_CNT=1,C_PROBE263_MU_CNT=1,C_PROBE264_MU_CNT=1,C_PROBE265_MU_CNT=1,C_PROBE266_MU_CNT=1,C_PROBE267_MU_CNT=1,C_PROBE268_MU_CNT=1,C_PROBE269_MU_CNT=1,C_PROBE270_MU_CNT=1,C_PROBE271_MU_CNT=1,C_PROBE272_MU_CNT=1,C_PROBE273_MU_CNT=1,C_PROBE274_MU_CNT=1,C_PROBE275_MU_CNT=1,C_PROBE276_MU_CNT=1,C_PROBE277_MU_CNT=1,C_PROBE278_MU_CNT=1,C_PROBE279_MU_CNT=1,C_PROBE280_MU_CNT=1,C_PROBE281_MU_CNT=1,C_PROBE282_MU_CNT=1,C_PROBE283_MU_CNT=1,C_PROBE284_MU_CNT=1,C_PROBE285_MU_CNT=1,C_PROBE286_MU_CNT=1,C_PROBE287_MU_CNT=1,C_PROBE288_MU_CNT=1,C_PROBE289_MU_CNT=1,C_PROBE290_MU_CNT=1,C_PROBE291_MU_CNT=1,C_PROBE292_MU_CNT=1,C_PROBE293_MU_CNT=1,C_PROBE294_MU_CNT=1,C_PROBE295_MU_CNT=1,C_PROBE296_MU_CNT=1,C_PROBE297_MU_CNT=1,C_PROBE298_MU_CNT=1,C_PROBE299_MU_CNT=1,C_PROBE300_MU_CNT=1,C_PROBE301_MU_CNT=1,C_PROBE302_MU_CNT=1,C_PROBE303_MU_CNT=1,C_PROBE304_MU_CNT=1,C_PROBE305_MU_CNT=1,C_PROBE306_MU_CNT=1,C_PROBE307_MU_CNT=1,C_PROBE308_MU_CNT=1,C_PROBE309_MU_CNT=1,C_PROBE310_MU_CNT=1,C_PROBE311_MU_CNT=1,C_PROBE312_MU_CNT=1,C_PROBE313_MU_CNT=1,C_PROBE314_MU_CNT=1,C_PROBE315_MU_CNT=1,C_PROBE316_MU_CNT=1,C_PROBE317_MU_CNT=1,C_PROBE318_MU_CNT=1,C_PROBE319_MU_CNT=1,C_PROBE320_MU_CNT=1,C_PROBE321_MU_CNT=1,C_PROBE322_MU_CNT=1,C_PROBE323_MU_CNT=1,C_PROBE324_MU_CNT=1,C_PROBE325_MU_CNT=1,C_PROBE326_MU_CNT=1,C_PROBE327_MU_CNT=1,C_PROBE328_MU_CNT=1,C_PROBE329_MU_CNT=1,\
C_PROBE330_MU_CNT=1,C_PROBE331_MU_CNT=1,C_PROBE332_MU_CNT=1,C_PROBE333_MU_CNT=1,C_PROBE334_MU_CNT=1,C_PROBE335_MU_CNT=1,C_PROBE336_MU_CNT=1,C_PROBE337_MU_CNT=1,C_PROBE338_MU_CNT=1,C_PROBE339_MU_CNT=1,C_PROBE340_MU_CNT=1,C_PROBE341_MU_CNT=1,C_PROBE342_MU_CNT=1,C_PROBE343_MU_CNT=1,C_PROBE344_MU_CNT=1,C_PROBE345_MU_CNT=1,C_PROBE346_MU_CNT=1,C_PROBE347_MU_CNT=1,C_PROBE348_MU_CNT=1,C_PROBE349_MU_CNT=1,C_PROBE350_MU_CNT=1,C_PROBE351_MU_CNT=1,C_PROBE352_MU_CNT=1,C_PROBE353_MU_CNT=1,C_PROBE354_MU_CNT=1,C_PROBE355_MU_CNT=1,C_PROBE356_MU_CNT=1,C_PROBE357_MU_CNT=1,C_PROBE358_MU_CNT=1,C_PROBE359_MU_CNT=1,C_PROBE360_MU_CNT=1,C_PROBE361_MU_CNT=1,C_PROBE362_MU_CNT=1,C_PROBE363_MU_CNT=1,C_PROBE364_MU_CNT=1,C_PROBE365_MU_CNT=1,C_PROBE366_MU_CNT=1,C_PROBE367_MU_CNT=1,C_PROBE368_MU_CNT=1,C_PROBE369_MU_CNT=1,C_PROBE370_MU_CNT=1,C_PROBE371_MU_CNT=1,C_PROBE372_MU_CNT=1,C_PROBE373_MU_CNT=1,C_PROBE374_MU_CNT=1,C_PROBE375_MU_CNT=1,C_PROBE376_MU_CNT=1,C_PROBE377_MU_CNT=1,C_PROBE378_MU_CNT=1,C_PROBE379_MU_CNT=1,C_PROBE380_MU_CNT=1,C_PROBE381_MU_CNT=1,C_PROBE382_MU_CNT=1,C_PROBE383_MU_CNT=1,C_PROBE384_MU_CNT=1,C_PROBE385_MU_CNT=1,C_PROBE386_MU_CNT=1,C_PROBE387_MU_CNT=1,C_PROBE388_MU_CNT=1,C_PROBE389_MU_CNT=1,C_PROBE390_MU_CNT=1,C_PROBE391_MU_CNT=1,C_PROBE392_MU_CNT=1,C_PROBE393_MU_CNT=1,C_PROBE394_MU_CNT=1,C_PROBE395_MU_CNT=1,C_PROBE396_MU_CNT=1,C_PROBE397_MU_CNT=1,C_PROBE398_MU_CNT=1,C_PROBE399_MU_CNT=1,C_PROBE400_MU_CNT=1,C_PROBE401_MU_CNT=1,C_PROBE402_MU_CNT=1,C_PROBE403_MU_CNT=1,C_PROBE404_MU_CNT=1,C_PROBE405_MU_CNT=1,C_PROBE406_MU_CNT=1,C_PROBE407_MU_CNT=1,C_PROBE408_MU_CNT=1,C_PROBE409_MU_CNT=1,C_PROBE410_MU_CNT=1,C_PROBE411_MU_CNT=1,C_PROBE412_MU_CNT=1,C_PROBE413_MU_CNT=1,C_PROBE414_MU_CNT=1,C_PROBE415_MU_CNT=1,C_PROBE416_MU_CNT=1,C_PROBE417_MU_CNT=1,C_PROBE418_MU_CNT=1,C_PROBE419_MU_CNT=1,C_PROBE420_MU_CNT=1,C_PROBE421_MU_CNT=1,C_PROBE422_MU_CNT=1,C_PROBE423_MU_CNT=1,C_PROBE424_MU_CNT=1,C_PROBE425_MU_CNT=1,C_PROBE426_MU_CNT=1,C_PROBE427_MU_CNT=1,C_PROBE428_MU_CNT=1,C_PROBE429_MU_CNT=1,\
C_PROBE430_MU_CNT=1,C_PROBE431_MU_CNT=1,C_PROBE432_MU_CNT=1,C_PROBE433_MU_CNT=1,C_PROBE434_MU_CNT=1,C_PROBE435_MU_CNT=1,C_PROBE436_MU_CNT=1,C_PROBE437_MU_CNT=1,C_PROBE438_MU_CNT=1,C_PROBE439_MU_CNT=1,C_PROBE440_MU_CNT=1,C_PROBE441_MU_CNT=1,C_PROBE442_MU_CNT=1,C_PROBE443_MU_CNT=1,C_PROBE444_MU_CNT=1,C_PROBE445_MU_CNT=1,C_PROBE446_MU_CNT=1,C_PROBE447_MU_CNT=1,C_PROBE448_MU_CNT=1,C_PROBE449_MU_CNT=1,C_PROBE450_MU_CNT=1,C_PROBE451_MU_CNT=1,C_PROBE452_MU_CNT=1,C_PROBE453_MU_CNT=1,C_PROBE454_MU_CNT=1,C_PROBE455_MU_CNT=1,C_PROBE456_MU_CNT=1,C_PROBE457_MU_CNT=1,C_PROBE458_MU_CNT=1,C_PROBE459_MU_CNT=1,C_PROBE460_MU_CNT=1,C_PROBE461_MU_CNT=1,C_PROBE462_MU_CNT=1,C_PROBE463_MU_CNT=1,C_PROBE464_MU_CNT=1,C_PROBE465_MU_CNT=1,C_PROBE466_MU_CNT=1,C_PROBE467_MU_CNT=1,C_PROBE468_MU_CNT=1,C_PROBE469_MU_CNT=1,C_PROBE470_MU_CNT=1,C_PROBE471_MU_CNT=1,C_PROBE472_MU_CNT=1,C_PROBE473_MU_CNT=1,C_PROBE474_MU_CNT=1,C_PROBE475_MU_CNT=1,C_PROBE476_MU_CNT=1,C_PROBE477_MU_CNT=1,C_PROBE478_MU_CNT=1,C_PROBE479_MU_CNT=1,C_PROBE480_MU_CNT=1,C_PROBE481_MU_CNT=1,C_PROBE482_MU_CNT=1,C_PROBE483_MU_CNT=1,C_PROBE484_MU_CNT=1,C_PROBE485_MU_CNT=1,C_PROBE486_MU_CNT=1,C_PROBE487_MU_CNT=1,C_PROBE488_MU_CNT=1,C_PROBE489_MU_CNT=1,C_PROBE490_MU_CNT=1,C_PROBE491_MU_CNT=1,C_PROBE492_MU_CNT=1,C_PROBE493_MU_CNT=1,C_PROBE494_MU_CNT=1,C_PROBE495_MU_CNT=1,C_PROBE496_MU_CNT=1,C_PROBE497_MU_CNT=1,C_PROBE498_MU_CNT=1,C_PROBE499_MU_CNT=1,C_PROBE500_MU_CNT=1,C_PROBE501_MU_CNT=1,C_PROBE502_MU_CNT=1,C_PROBE503_MU_CNT=1,C_PROBE504_MU_CNT=1,C_PROBE505_MU_CNT=1,C_PROBE506_MU_CNT=1,C_PROBE507_MU_CNT=1,C_PROBE508_MU_CNT=1,C_PROBE509_MU_CNT=1,C_PROBE510_MU_CNT=1,C_PROBE511_MU_CNT=1,C_PROBE512_MU_CNT=1,C_PROBE513_MU_CNT=1,C_PROBE514_MU_CNT=1,C_PROBE515_MU_CNT=1,C_PROBE516_MU_CNT=1,C_PROBE517_MU_CNT=1,C_PROBE518_MU_CNT=1,C_PROBE519_MU_CNT=1,C_PROBE520_MU_CNT=1,C_PROBE521_MU_CNT=1,C_PROBE522_MU_CNT=1,C_PROBE523_MU_CNT=1,C_PROBE524_MU_CNT=1,C_PROBE525_MU_CNT=1,C_PROBE526_MU_CNT=1,C_PROBE527_MU_CNT=1,C_PROBE528_MU_CNT=1,C_PROBE529_MU_CNT=1,\
C_PROBE530_MU_CNT=1,C_PROBE531_MU_CNT=1,C_PROBE532_MU_CNT=1,C_PROBE533_MU_CNT=1,C_PROBE534_MU_CNT=1,C_PROBE535_MU_CNT=1,C_PROBE536_MU_CNT=1,C_PROBE537_MU_CNT=1,C_PROBE538_MU_CNT=1,C_PROBE539_MU_CNT=1,C_PROBE540_MU_CNT=1,C_PROBE541_MU_CNT=1,C_PROBE542_MU_CNT=1,C_PROBE543_MU_CNT=1,C_PROBE544_MU_CNT=1,C_PROBE545_MU_CNT=1,C_PROBE546_MU_CNT=1,C_PROBE547_MU_CNT=1,C_PROBE548_MU_CNT=1,C_PROBE549_MU_CNT=1,C_PROBE550_MU_CNT=1,C_PROBE551_MU_CNT=1,C_PROBE552_MU_CNT=1,C_PROBE553_MU_CNT=1,C_PROBE554_MU_CNT=1,C_PROBE555_MU_CNT=1,C_PROBE556_MU_CNT=1,C_PROBE557_MU_CNT=1,C_PROBE558_MU_CNT=1,C_PROBE559_MU_CNT=1,C_PROBE560_MU_CNT=1,C_PROBE561_MU_CNT=1,C_PROBE562_MU_CNT=1,C_PROBE563_MU_CNT=1,C_PROBE564_MU_CNT=1,C_PROBE565_MU_CNT=1,C_PROBE566_MU_CNT=1,C_PROBE567_MU_CNT=1,C_PROBE568_MU_CNT=1,C_PROBE569_MU_CNT=1,C_PROBE570_MU_CNT=1,C_PROBE571_MU_CNT=1,C_PROBE572_MU_CNT=1,C_PROBE573_MU_CNT=1,C_PROBE574_MU_CNT=1,C_PROBE575_MU_CNT=1,C_PROBE576_MU_CNT=1,C_PROBE577_MU_CNT=1,C_PROBE578_MU_CNT=1,C_PROBE579_MU_CNT=1,C_PROBE580_MU_CNT=1,C_PROBE581_MU_CNT=1,C_PROBE582_MU_CNT=1,C_PROBE583_MU_CNT=1,C_PROBE584_MU_CNT=1,C_PROBE585_MU_CNT=1,C_PROBE586_MU_CNT=1,C_PROBE587_MU_CNT=1,C_PROBE588_MU_CNT=1,C_PROBE589_MU_CNT=1,C_PROBE590_MU_CNT=1,C_PROBE591_MU_CNT=1,C_PROBE592_MU_CNT=1,C_PROBE593_MU_CNT=1,C_PROBE594_MU_CNT=1,C_PROBE595_MU_CNT=1,C_PROBE596_MU_CNT=1,C_PROBE597_MU_CNT=1,C_PROBE598_MU_CNT=1,C_PROBE599_MU_CNT=1,C_PROBE600_MU_CNT=1,C_PROBE601_MU_CNT=1,C_PROBE602_MU_CNT=1,C_PROBE603_MU_CNT=1,C_PROBE604_MU_CNT=1,C_PROBE605_MU_CNT=1,C_PROBE606_MU_CNT=1,C_PROBE607_MU_CNT=1,C_PROBE608_MU_CNT=1,C_PROBE609_MU_CNT=1,C_PROBE610_MU_CNT=1,C_PROBE611_MU_CNT=1,C_PROBE612_MU_CNT=1,C_PROBE613_MU_CNT=1,C_PROBE614_MU_CNT=1,C_PROBE615_MU_CNT=1,C_PROBE616_MU_CNT=1,C_PROBE617_MU_CNT=1,C_PROBE618_MU_CNT=1,C_PROBE619_MU_CNT=1,C_PROBE620_MU_CNT=1,C_PROBE621_MU_CNT=1,C_PROBE622_MU_CNT=1,C_PROBE623_MU_CNT=1,C_PROBE624_MU_CNT=1,C_PROBE625_MU_CNT=1,C_PROBE626_MU_CNT=1,C_PROBE627_MU_CNT=1,C_PROBE628_MU_CNT=1,C_PROBE629_MU_CNT=1,\
C_PROBE630_MU_CNT=1,C_PROBE631_MU_CNT=1,C_PROBE632_MU_CNT=1,C_PROBE633_MU_CNT=1,C_PROBE634_MU_CNT=1,C_PROBE635_MU_CNT=1,C_PROBE636_MU_CNT=1,C_PROBE637_MU_CNT=1,C_PROBE638_MU_CNT=1,C_PROBE639_MU_CNT=1,C_PROBE640_MU_CNT=1,C_PROBE641_MU_CNT=1,C_PROBE642_MU_CNT=1,C_PROBE643_MU_CNT=1,C_PROBE644_MU_CNT=1,C_PROBE645_MU_CNT=1,C_PROBE646_MU_CNT=1,C_PROBE647_MU_CNT=1,C_PROBE648_MU_CNT=1,C_PROBE649_MU_CNT=1,C_PROBE650_MU_CNT=1,C_PROBE651_MU_CNT=1,C_PROBE652_MU_CNT=1,C_PROBE653_MU_CNT=1,C_PROBE654_MU_CNT=1,C_PROBE655_MU_CNT=1,C_PROBE656_MU_CNT=1,C_PROBE657_MU_CNT=1,C_PROBE658_MU_CNT=1,C_PROBE659_MU_CNT=1,C_PROBE660_MU_CNT=1,C_PROBE661_MU_CNT=1,C_PROBE662_MU_CNT=1,C_PROBE663_MU_CNT=1,C_PROBE664_MU_CNT=1,C_PROBE665_MU_CNT=1,C_PROBE666_MU_CNT=1,C_PROBE667_MU_CNT=1,C_PROBE668_MU_CNT=1,C_PROBE669_MU_CNT=1,C_PROBE670_MU_CNT=1,C_PROBE671_MU_CNT=1,C_PROBE672_MU_CNT=1,C_PROBE673_MU_CNT=1,C_PROBE674_MU_CNT=1,C_PROBE675_MU_CNT=1,C_PROBE676_MU_CNT=1,C_PROBE677_MU_CNT=1,C_PROBE678_MU_CNT=1,C_PROBE679_MU_CNT=1,C_PROBE680_MU_CNT=1,C_PROBE681_MU_CNT=1,C_PROBE682_MU_CNT=1,C_PROBE683_MU_CNT=1,C_PROBE684_MU_CNT=1,C_PROBE685_MU_CNT=1,C_PROBE686_MU_CNT=1,C_PROBE687_MU_CNT=1,C_PROBE688_MU_CNT=1,C_PROBE689_MU_CNT=1,C_PROBE690_MU_CNT=1,C_PROBE691_MU_CNT=1,C_PROBE692_MU_CNT=1,C_PROBE693_MU_CNT=1,C_PROBE694_MU_CNT=1,C_PROBE695_MU_CNT=1,C_PROBE696_MU_CNT=1,C_PROBE697_MU_CNT=1,C_PROBE698_MU_CNT=1,C_PROBE699_MU_CNT=1,C_PROBE700_MU_CNT=1,C_PROBE701_MU_CNT=1,C_PROBE702_MU_CNT=1,C_PROBE703_MU_CNT=1,C_PROBE704_MU_CNT=1,C_PROBE705_MU_CNT=1,C_PROBE706_MU_CNT=1,C_PROBE707_MU_CNT=1,C_PROBE708_MU_CNT=1,C_PROBE709_MU_CNT=1,C_PROBE710_MU_CNT=1,C_PROBE711_MU_CNT=1,C_PROBE712_MU_CNT=1,C_PROBE713_MU_CNT=1,C_PROBE714_MU_CNT=1,C_PROBE715_MU_CNT=1,C_PROBE716_MU_CNT=1,C_PROBE717_MU_CNT=1,C_PROBE718_MU_CNT=1,C_PROBE719_MU_CNT=1,C_PROBE720_MU_CNT=1,C_PROBE721_MU_CNT=1,C_PROBE722_MU_CNT=1,C_PROBE723_MU_CNT=1,C_PROBE724_MU_CNT=1,C_PROBE725_MU_CNT=1,C_PROBE726_MU_CNT=1,C_PROBE727_MU_CNT=1,C_PROBE728_MU_CNT=1,C_PROBE729_MU_CNT=1,\
C_PROBE730_MU_CNT=1,C_PROBE731_MU_CNT=1,C_PROBE732_MU_CNT=1,C_PROBE733_MU_CNT=1,C_PROBE734_MU_CNT=1,C_PROBE735_MU_CNT=1,C_PROBE736_MU_CNT=1,C_PROBE737_MU_CNT=1,C_PROBE738_MU_CNT=1,C_PROBE739_MU_CNT=1,C_PROBE740_MU_CNT=1,C_PROBE741_MU_CNT=1,C_PROBE742_MU_CNT=1,C_PROBE743_MU_CNT=1,C_PROBE744_MU_CNT=1,C_PROBE745_MU_CNT=1,C_PROBE746_MU_CNT=1,C_PROBE747_MU_CNT=1,C_PROBE748_MU_CNT=1,C_PROBE749_MU_CNT=1,C_PROBE750_MU_CNT=1,C_PROBE751_MU_CNT=1,C_PROBE752_MU_CNT=1,C_PROBE753_MU_CNT=1,C_PROBE754_MU_CNT=1,C_PROBE755_MU_CNT=1,C_PROBE756_MU_CNT=1,C_PROBE757_MU_CNT=1,C_PROBE758_MU_CNT=1,C_PROBE759_MU_CNT=1,C_PROBE760_MU_CNT=1,C_PROBE761_MU_CNT=1,C_PROBE762_MU_CNT=1,C_PROBE763_MU_CNT=1,C_PROBE764_MU_CNT=1,C_PROBE765_MU_CNT=1,C_PROBE766_MU_CNT=1,C_PROBE767_MU_CNT=1,C_PROBE768_MU_CNT=1,C_PROBE769_MU_CNT=1,C_PROBE770_MU_CNT=1,C_PROBE771_MU_CNT=1,C_PROBE772_MU_CNT=1,C_PROBE773_MU_CNT=1,C_PROBE774_MU_CNT=1,C_PROBE775_MU_CNT=1,C_PROBE776_MU_CNT=1,C_PROBE777_MU_CNT=1,C_PROBE778_MU_CNT=1,C_PROBE779_MU_CNT=1,C_PROBE780_MU_CNT=1,C_PROBE781_MU_CNT=1,C_PROBE782_MU_CNT=1,C_PROBE783_MU_CNT=1,C_PROBE784_MU_CNT=1,C_PROBE785_MU_CNT=1,C_PROBE786_MU_CNT=1,C_PROBE787_MU_CNT=1,C_PROBE788_MU_CNT=1,C_PROBE789_MU_CNT=1,C_PROBE790_MU_CNT=1,C_PROBE791_MU_CNT=1,C_PROBE792_MU_CNT=1,C_PROBE793_MU_CNT=1,C_PROBE794_MU_CNT=1,C_PROBE795_MU_CNT=1,C_PROBE796_MU_CNT=1,C_PROBE797_MU_CNT=1,C_PROBE798_MU_CNT=1,C_PROBE799_MU_CNT=1,C_PROBE800_MU_CNT=1,C_PROBE801_MU_CNT=1,C_PROBE802_MU_CNT=1,C_PROBE803_MU_CNT=1,C_PROBE804_MU_CNT=1,C_PROBE805_MU_CNT=1,C_PROBE806_MU_CNT=1,C_PROBE807_MU_CNT=1,C_PROBE808_MU_CNT=1,C_PROBE809_MU_CNT=1,C_PROBE810_MU_CNT=1,C_PROBE811_MU_CNT=1,C_PROBE812_MU_CNT=1,C_PROBE813_MU_CNT=1,C_PROBE814_MU_CNT=1,C_PROBE815_MU_CNT=1,C_PROBE816_MU_CNT=1,C_PROBE817_MU_CNT=1,C_PROBE818_MU_CNT=1,C_PROBE819_MU_CNT=1,C_PROBE820_MU_CNT=1,C_PROBE821_MU_CNT=1,C_PROBE822_MU_CNT=1,C_PROBE823_MU_CNT=1,C_PROBE824_MU_CNT=1,C_PROBE825_MU_CNT=1,C_PROBE826_MU_CNT=1,C_PROBE827_MU_CNT=1,C_PROBE828_MU_CNT=1,C_PROBE829_MU_CNT=1,\
C_PROBE830_MU_CNT=1,C_PROBE831_MU_CNT=1,C_PROBE832_MU_CNT=1,C_PROBE833_MU_CNT=1,C_PROBE834_MU_CNT=1,C_PROBE835_MU_CNT=1,C_PROBE836_MU_CNT=1,C_PROBE837_MU_CNT=1,C_PROBE838_MU_CNT=1,C_PROBE839_MU_CNT=1,C_PROBE840_MU_CNT=1,C_PROBE841_MU_CNT=1,C_PROBE842_MU_CNT=1,C_PROBE843_MU_CNT=1,C_PROBE844_MU_CNT=1,C_PROBE845_MU_CNT=1,C_PROBE846_MU_CNT=1,C_PROBE847_MU_CNT=1,C_PROBE848_MU_CNT=1,C_PROBE849_MU_CNT=1,C_PROBE850_MU_CNT=1,C_PROBE851_MU_CNT=1,C_PROBE852_MU_CNT=1,C_PROBE853_MU_CNT=1,C_PROBE854_MU_CNT=1,C_PROBE855_MU_CNT=1,C_PROBE856_MU_CNT=1,C_PROBE857_MU_CNT=1,C_PROBE858_MU_CNT=1,C_PROBE859_MU_CNT=1,C_PROBE860_MU_CNT=1,C_PROBE861_MU_CNT=1,C_PROBE862_MU_CNT=1,C_PROBE863_MU_CNT=1,C_PROBE864_MU_CNT=1,C_PROBE865_MU_CNT=1,C_PROBE866_MU_CNT=1,C_PROBE867_MU_CNT=1,C_PROBE868_MU_CNT=1,C_PROBE869_MU_CNT=1,C_PROBE870_MU_CNT=1,C_PROBE871_MU_CNT=1,C_PROBE872_MU_CNT=1,C_PROBE873_MU_CNT=1,C_PROBE874_MU_CNT=1,C_PROBE875_MU_CNT=1,C_PROBE876_MU_CNT=1,C_PROBE877_MU_CNT=1,C_PROBE878_MU_CNT=1,C_PROBE879_MU_CNT=1,C_PROBE880_MU_CNT=1,C_PROBE881_MU_CNT=1,C_PROBE882_MU_CNT=1,C_PROBE883_MU_CNT=1,C_PROBE884_MU_CNT=1,C_PROBE885_MU_CNT=1,C_PROBE886_MU_CNT=1,C_PROBE887_MU_CNT=1,C_PROBE888_MU_CNT=1,C_PROBE889_MU_CNT=1,C_PROBE890_MU_CNT=1,C_PROBE891_MU_CNT=1,C_PROBE892_MU_CNT=1,C_PROBE893_MU_CNT=1,C_PROBE894_MU_CNT=1,C_PROBE895_MU_CNT=1,C_PROBE896_MU_CNT=1,C_PROBE897_MU_CNT=1,C_PROBE898_MU_CNT=1,C_PROBE899_MU_CNT=1,C_PROBE900_MU_CNT=1,C_PROBE901_MU_CNT=1,C_PROBE902_MU_CNT=1,C_PROBE903_MU_CNT=1,C_PROBE904_MU_CNT=1,C_PROBE905_MU_CNT=1,C_PROBE906_MU_CNT=1,C_PROBE907_MU_CNT=1,C_PROBE908_MU_CNT=1,C_PROBE909_MU_CNT=1,C_PROBE910_MU_CNT=1,C_PROBE911_MU_CNT=1,C_PROBE912_MU_CNT=1,C_PROBE913_MU_CNT=1,C_PROBE914_MU_CNT=1,C_PROBE915_MU_CNT=1,C_PROBE916_MU_CNT=1,C_PROBE917_MU_CNT=1,C_PROBE918_MU_CNT=1,C_PROBE919_MU_CNT=1,C_PROBE920_MU_CNT=1,C_PROBE921_MU_CNT=1,C_PROBE922_MU_CNT=1,C_PROBE923_MU_CNT=1,C_PROBE924_MU_CNT=1,C_PROBE925_MU_CNT=1,C_PROBE926_MU_CNT=1,C_PROBE927_MU_CNT=1,C_PROBE928_MU_CNT=1,C_PROBE929_MU_CNT=1,\
C_PROBE930_MU_CNT=1,C_PROBE931_MU_CNT=1,C_PROBE932_MU_CNT=1,C_PROBE933_MU_CNT=1,C_PROBE934_MU_CNT=1,C_PROBE935_MU_CNT=1,C_PROBE936_MU_CNT=1,C_PROBE937_MU_CNT=1,C_PROBE938_MU_CNT=1,C_PROBE939_MU_CNT=1,C_PROBE940_MU_CNT=1,C_PROBE941_MU_CNT=1,C_PROBE942_MU_CNT=1,C_PROBE943_MU_CNT=1,C_PROBE944_MU_CNT=1,C_PROBE945_MU_CNT=1,C_PROBE946_MU_CNT=1,C_PROBE947_MU_CNT=1,C_PROBE948_MU_CNT=1,C_PROBE949_MU_CNT=1,C_PROBE950_MU_CNT=1,C_PROBE951_MU_CNT=1,C_PROBE952_MU_CNT=1,C_PROBE953_MU_CNT=1,C_PROBE954_MU_CNT=1,C_PROBE955_MU_CNT=1,C_PROBE956_MU_CNT=1,C_PROBE957_MU_CNT=1,C_PROBE958_MU_CNT=1,C_PROBE959_MU_CNT=1,C_PROBE960_MU_CNT=1,C_PROBE961_MU_CNT=1,C_PROBE962_MU_CNT=1,C_PROBE963_MU_CNT=1,C_PROBE964_MU_CNT=1,C_PROBE965_MU_CNT=1,C_PROBE966_MU_CNT=1,C_PROBE967_MU_CNT=1,C_PROBE968_MU_CNT=1,C_PROBE969_MU_CNT=1,C_PROBE970_MU_CNT=1,C_PROBE971_MU_CNT=1,C_PROBE972_MU_CNT=1,C_PROBE973_MU_CNT=1,C_PROBE974_MU_CNT=1,C_PROBE975_MU_CNT=1,C_PROBE976_MU_CNT=1,C_PROBE977_MU_CNT=1,C_PROBE978_MU_CNT=1,C_PROBE979_MU_CNT=1,C_PROBE980_MU_CNT=1,C_PROBE981_MU_CNT=1,C_PROBE982_MU_CNT=1,C_PROBE983_MU_CNT=1,C_PROBE984_MU_CNT=1,C_PROBE985_MU_CNT=1,C_PROBE986_MU_CNT=1,C_PROBE987_MU_CNT=1,C_PROBE988_MU_CNT=1,C_PROBE989_MU_CNT=1,C_PROBE990_MU_CNT=1,C_PROBE991_MU_CNT=1,C_PROBE992_MU_CNT=1,C_PROBE993_MU_CNT=1,C_PROBE994_MU_CNT=1,C_PROBE995_MU_CNT=1,C_PROBE996_MU_CNT=1,C_PROBE997_MU_CNT=1,C_PROBE998_MU_CNT=1,C_PROBE999_MU_CNT=1,C_PROBE1000_MU_CNT=1,C_PROBE1001_MU_CNT=1,C_PROBE1002_MU_CNT=1,C_PROBE1003_MU_CNT=1,C_PROBE1004_MU_CNT=1,C_PROBE1005_MU_CNT=1,C_PROBE1006_MU_CNT=1,C_PROBE1007_MU_CNT=1,C_PROBE1008_MU_CNT=1,C_PROBE1009_MU_CNT=1,C_PROBE1010_MU_CNT=1,C_PROBE1011_MU_CNT=1,C_PROBE1012_MU_CNT=1,C_PROBE1013_MU_CNT=1,C_PROBE1014_MU_CNT=1,C_PROBE1015_MU_CNT=1,C_PROBE1016_MU_CNT=1,C_PROBE1017_MU_CNT=1,C_PROBE1018_MU_CNT=1,C_PROBE1019_MU_CNT=1,C_PROBE1020_MU_CNT=1,C_PROBE1021_MU_CNT=1,C_PROBE1022_MU_CNT=1,C_PROBE1023_MU_CNT=1,C_PROBE0_TYPE=1,C_PROBE1_TYPE=0,C_PROBE2_TYPE=0,C_PROBE3_TYPE=0,C_PROBE4_TYPE=0,C_PROBE5_TYPE=1,\
C_PROBE6_TYPE=0,C_PROBE7_TYPE=1,C_PROBE8_TYPE=0,C_PROBE9_TYPE=0,C_PROBE10_TYPE=0,C_PROBE11_TYPE=0,C_PROBE12_TYPE=0,C_PROBE13_TYPE=0,C_PROBE14_TYPE=0,C_PROBE15_TYPE=0,C_PROBE16_TYPE=0,C_PROBE17_TYPE=0,C_PROBE18_TYPE=0,C_PROBE19_TYPE=0,C_PROBE20_TYPE=0,C_PROBE21_TYPE=0,C_PROBE22_TYPE=0,C_PROBE23_TYPE=0,C_PROBE24_TYPE=1,C_PROBE25_TYPE=1,C_PROBE26_TYPE=0,C_PROBE27_TYPE=0,C_PROBE28_TYPE=1,C_PROBE29_TYPE=1,C_PROBE30_TYPE=1,C_PROBE31_TYPE=1,C_PROBE32_TYPE=1,C_PROBE33_TYPE=1,C_PROBE34_TYPE=1,C_PROBE35_TYPE=1,C_PROBE36_TYPE=1,C_PROBE37_TYPE=1,C_PROBE38_TYPE=1,C_PROBE39_TYPE=1,C_PROBE40_TYPE=1,C_PROBE41_TYPE=1,C_PROBE42_TYPE=1,C_PROBE43_TYPE=1,C_PROBE44_TYPE=1,C_PROBE45_TYPE=1,C_PROBE46_TYPE=1,C_PROBE47_TYPE=1,C_PROBE48_TYPE=1,C_PROBE49_TYPE=1,C_PROBE50_TYPE=1,C_PROBE51_TYPE=1,C_PROBE52_TYPE=1,C_PROBE53_TYPE=1,C_PROBE54_TYPE=1,C_PROBE55_TYPE=1,C_PROBE56_TYPE=1,C_PROBE57_TYPE=1,C_PROBE58_TYPE=1,C_PROBE59_TYPE=1,C_PROBE60_TYPE=1,C_PROBE61_TYPE=1,C_PROBE62_TYPE=1,C_PROBE63_TYPE=1,C_PROBE64_TYPE=1,C_PROBE65_TYPE=1,C_PROBE66_TYPE=1,C_PROBE67_TYPE=1,C_PROBE68_TYPE=1,C_PROBE69_TYPE=1,C_PROBE70_TYPE=1,C_PROBE71_TYPE=1,C_PROBE72_TYPE=1,C_PROBE73_TYPE=1,C_PROBE74_TYPE=1,C_PROBE75_TYPE=1,C_PROBE76_TYPE=1,C_PROBE77_TYPE=1,C_PROBE78_TYPE=1,C_PROBE79_TYPE=1,C_PROBE80_TYPE=1,C_PROBE81_TYPE=1,C_PROBE82_TYPE=1,C_PROBE83_TYPE=1,C_PROBE84_TYPE=1,C_PROBE85_TYPE=1,C_PROBE86_TYPE=1,C_PROBE87_TYPE=1,C_PROBE88_TYPE=1,C_PROBE89_TYPE=1,C_PROBE90_TYPE=1,C_PROBE91_TYPE=1,C_PROBE92_TYPE=1,C_PROBE93_TYPE=1,C_PROBE94_TYPE=1,C_PROBE95_TYPE=1,C_PROBE96_TYPE=1,C_PROBE97_TYPE=1,C_PROBE98_TYPE=1,C_PROBE99_TYPE=1,C_PROBE100_TYPE=1,C_PROBE101_TYPE=1,C_PROBE102_TYPE=1,C_PROBE103_TYPE=1,C_PROBE104_TYPE=1,C_PROBE105_TYPE=1,\
C_PROBE106_TYPE=1,C_PROBE107_TYPE=1,C_PROBE108_TYPE=1,C_PROBE109_TYPE=1,C_PROBE110_TYPE=1,C_PROBE111_TYPE=1,C_PROBE112_TYPE=1,C_PROBE113_TYPE=1,C_PROBE114_TYPE=1,C_PROBE115_TYPE=1,C_PROBE116_TYPE=1,C_PROBE117_TYPE=1,C_PROBE118_TYPE=1,C_PROBE119_TYPE=1,C_PROBE120_TYPE=1,C_PROBE121_TYPE=1,C_PROBE122_TYPE=1,C_PROBE123_TYPE=1,C_PROBE124_TYPE=1,C_PROBE125_TYPE=1,C_PROBE126_TYPE=1,C_PROBE127_TYPE=1,C_PROBE128_TYPE=1,C_PROBE129_TYPE=1,C_PROBE130_TYPE=1,C_PROBE131_TYPE=1,C_PROBE132_TYPE=1,C_PROBE133_TYPE=1,C_PROBE134_TYPE=1,C_PROBE135_TYPE=1,C_PROBE136_TYPE=1,C_PROBE137_TYPE=1,C_PROBE138_TYPE=1,C_PROBE139_TYPE=1,C_PROBE140_TYPE=1,C_PROBE141_TYPE=1,C_PROBE142_TYPE=1,C_PROBE143_TYPE=1,C_PROBE144_TYPE=1,C_PROBE145_TYPE=1,C_PROBE146_TYPE=1,C_PROBE147_TYPE=1,C_PROBE148_TYPE=1,C_PROBE149_TYPE=1,C_PROBE150_TYPE=1,C_PROBE151_TYPE=1,C_PROBE152_TYPE=1,C_PROBE153_TYPE=1,C_PROBE154_TYPE=1,C_PROBE155_TYPE=1,C_PROBE156_TYPE=1,C_PROBE157_TYPE=1,C_PROBE158_TYPE=1,C_PROBE159_TYPE=1,C_PROBE160_TYPE=1,C_PROBE161_TYPE=1,C_PROBE162_TYPE=1,C_PROBE163_TYPE=1,C_PROBE164_TYPE=1,C_PROBE165_TYPE=1,C_PROBE166_TYPE=1,C_PROBE167_TYPE=1,C_PROBE168_TYPE=1,C_PROBE169_TYPE=1,C_PROBE170_TYPE=1,C_PROBE171_TYPE=1,C_PROBE172_TYPE=1,C_PROBE173_TYPE=1,C_PROBE174_TYPE=1,C_PROBE175_TYPE=1,C_PROBE176_TYPE=1,C_PROBE177_TYPE=1,C_PROBE178_TYPE=1,C_PROBE179_TYPE=1,C_PROBE180_TYPE=1,C_PROBE181_TYPE=1,C_PROBE182_TYPE=1,C_PROBE183_TYPE=1,C_PROBE184_TYPE=1,C_PROBE185_TYPE=1,C_PROBE186_TYPE=1,C_PROBE187_TYPE=1,C_PROBE188_TYPE=1,C_PROBE189_TYPE=1,C_PROBE190_TYPE=1,C_PROBE191_TYPE=1,C_PROBE192_TYPE=1,C_PROBE193_TYPE=1,C_PROBE194_TYPE=1,C_PROBE195_TYPE=1,C_PROBE196_TYPE=1,C_PROBE197_TYPE=1,C_PROBE198_TYPE=1,C_PROBE199_TYPE=1,C_PROBE200_TYPE=1,C_PROBE201_TYPE=1,C_PROBE202_TYPE=1,C_PROBE203_TYPE=1,C_PROBE204_TYPE=1,C_PROBE205_TYPE=1,\
C_PROBE206_TYPE=1,C_PROBE207_TYPE=1,C_PROBE208_TYPE=1,C_PROBE209_TYPE=1,C_PROBE210_TYPE=1,C_PROBE211_TYPE=1,C_PROBE212_TYPE=1,C_PROBE213_TYPE=1,C_PROBE214_TYPE=1,C_PROBE215_TYPE=1,C_PROBE216_TYPE=1,C_PROBE217_TYPE=1,C_PROBE218_TYPE=1,C_PROBE219_TYPE=1,C_PROBE220_TYPE=1,C_PROBE221_TYPE=1,C_PROBE222_TYPE=1,C_PROBE223_TYPE=1,C_PROBE224_TYPE=1,C_PROBE225_TYPE=1,C_PROBE226_TYPE=1,C_PROBE227_TYPE=1,C_PROBE228_TYPE=1,C_PROBE229_TYPE=1,C_PROBE230_TYPE=1,C_PROBE231_TYPE=1,C_PROBE232_TYPE=1,C_PROBE233_TYPE=1,C_PROBE234_TYPE=1,C_PROBE235_TYPE=1,C_PROBE236_TYPE=1,C_PROBE237_TYPE=1,C_PROBE238_TYPE=1,C_PROBE239_TYPE=1,C_PROBE240_TYPE=1,C_PROBE241_TYPE=1,C_PROBE242_TYPE=1,C_PROBE243_TYPE=1,C_PROBE244_TYPE=1,C_PROBE245_TYPE=1,C_PROBE246_TYPE=1,C_PROBE247_TYPE=1,C_PROBE248_TYPE=1,C_PROBE249_TYPE=1,C_PROBE250_TYPE=1,C_PROBE251_TYPE=1,C_PROBE252_TYPE=1,C_PROBE253_TYPE=1,C_PROBE254_TYPE=1,C_PROBE255_TYPE=1,C_PROBE256_TYPE=1,C_PROBE257_TYPE=1,C_PROBE258_TYPE=1,C_PROBE259_TYPE=1,C_PROBE260_TYPE=1,C_PROBE261_TYPE=1,C_PROBE262_TYPE=1,C_PROBE263_TYPE=1,C_PROBE264_TYPE=1,C_PROBE265_TYPE=1,C_PROBE266_TYPE=1,C_PROBE267_TYPE=1,C_PROBE268_TYPE=1,C_PROBE269_TYPE=1,C_PROBE270_TYPE=1,C_PROBE271_TYPE=1,C_PROBE272_TYPE=1,C_PROBE273_TYPE=1,C_PROBE274_TYPE=1,C_PROBE275_TYPE=1,C_PROBE276_TYPE=1,C_PROBE277_TYPE=1,C_PROBE278_TYPE=1,C_PROBE279_TYPE=1,C_PROBE280_TYPE=1,C_PROBE281_TYPE=1,C_PROBE282_TYPE=1,C_PROBE283_TYPE=1,C_PROBE284_TYPE=1,C_PROBE285_TYPE=1,C_PROBE286_TYPE=1,C_PROBE287_TYPE=1,C_PROBE288_TYPE=1,C_PROBE289_TYPE=1,C_PROBE290_TYPE=1,C_PROBE291_TYPE=1,C_PROBE292_TYPE=1,C_PROBE293_TYPE=1,C_PROBE294_TYPE=1,C_PROBE295_TYPE=1,C_PROBE296_TYPE=1,C_PROBE297_TYPE=1,C_PROBE298_TYPE=1,C_PROBE299_TYPE=1,C_PROBE300_TYPE=1,C_PROBE301_TYPE=1,C_PROBE302_TYPE=1,C_PROBE303_TYPE=1,C_PROBE304_TYPE=1,C_PROBE305_TYPE=1,\
C_PROBE306_TYPE=1,C_PROBE307_TYPE=1,C_PROBE308_TYPE=1,C_PROBE309_TYPE=1,C_PROBE310_TYPE=1,C_PROBE311_TYPE=1,C_PROBE312_TYPE=1,C_PROBE313_TYPE=1,C_PROBE314_TYPE=1,C_PROBE315_TYPE=1,C_PROBE316_TYPE=1,C_PROBE317_TYPE=1,C_PROBE318_TYPE=1,C_PROBE319_TYPE=1,C_PROBE320_TYPE=1,C_PROBE321_TYPE=1,C_PROBE322_TYPE=1,C_PROBE323_TYPE=1,C_PROBE324_TYPE=1,C_PROBE325_TYPE=1,C_PROBE326_TYPE=1,C_PROBE327_TYPE=1,C_PROBE328_TYPE=1,C_PROBE329_TYPE=1,C_PROBE330_TYPE=1,C_PROBE331_TYPE=1,C_PROBE332_TYPE=1,C_PROBE333_TYPE=1,C_PROBE334_TYPE=1,C_PROBE335_TYPE=1,C_PROBE336_TYPE=1,C_PROBE337_TYPE=1,C_PROBE338_TYPE=1,C_PROBE339_TYPE=1,C_PROBE340_TYPE=1,C_PROBE341_TYPE=1,C_PROBE342_TYPE=1,C_PROBE343_TYPE=1,C_PROBE344_TYPE=1,C_PROBE345_TYPE=1,C_PROBE346_TYPE=1,C_PROBE347_TYPE=1,C_PROBE348_TYPE=1,C_PROBE349_TYPE=1,C_PROBE350_TYPE=1,C_PROBE351_TYPE=1,C_PROBE352_TYPE=1,C_PROBE353_TYPE=1,C_PROBE354_TYPE=1,C_PROBE355_TYPE=1,C_PROBE356_TYPE=1,C_PROBE357_TYPE=1,C_PROBE358_TYPE=1,C_PROBE359_TYPE=1,C_PROBE360_TYPE=1,C_PROBE361_TYPE=1,C_PROBE362_TYPE=1,C_PROBE363_TYPE=1,C_PROBE364_TYPE=1,C_PROBE365_TYPE=1,C_PROBE366_TYPE=1,C_PROBE367_TYPE=1,C_PROBE368_TYPE=1,C_PROBE369_TYPE=1,C_PROBE370_TYPE=1,C_PROBE371_TYPE=1,C_PROBE372_TYPE=1,C_PROBE373_TYPE=1,C_PROBE374_TYPE=1,C_PROBE375_TYPE=1,C_PROBE376_TYPE=1,C_PROBE377_TYPE=1,C_PROBE378_TYPE=1,C_PROBE379_TYPE=1,C_PROBE380_TYPE=1,C_PROBE381_TYPE=1,C_PROBE382_TYPE=1,C_PROBE383_TYPE=1,C_PROBE384_TYPE=1,C_PROBE385_TYPE=1,C_PROBE386_TYPE=1,C_PROBE387_TYPE=1,C_PROBE388_TYPE=1,C_PROBE389_TYPE=1,C_PROBE390_TYPE=1,C_PROBE391_TYPE=1,C_PROBE392_TYPE=1,C_PROBE393_TYPE=1,C_PROBE394_TYPE=1,C_PROBE395_TYPE=1,C_PROBE396_TYPE=1,C_PROBE397_TYPE=1,C_PROBE398_TYPE=1,C_PROBE399_TYPE=1,C_PROBE400_TYPE=1,C_PROBE401_TYPE=1,C_PROBE402_TYPE=1,C_PROBE403_TYPE=1,C_PROBE404_TYPE=1,C_PROBE405_TYPE=1,\
C_PROBE406_TYPE=1,C_PROBE407_TYPE=1,C_PROBE408_TYPE=1,C_PROBE409_TYPE=1,C_PROBE410_TYPE=1,C_PROBE411_TYPE=1,C_PROBE412_TYPE=1,C_PROBE413_TYPE=1,C_PROBE414_TYPE=1,C_PROBE415_TYPE=1,C_PROBE416_TYPE=1,C_PROBE417_TYPE=1,C_PROBE418_TYPE=1,C_PROBE419_TYPE=1,C_PROBE420_TYPE=1,C_PROBE421_TYPE=1,C_PROBE422_TYPE=1,C_PROBE423_TYPE=1,C_PROBE424_TYPE=1,C_PROBE425_TYPE=1,C_PROBE426_TYPE=1,C_PROBE427_TYPE=1,C_PROBE428_TYPE=1,C_PROBE429_TYPE=1,C_PROBE430_TYPE=1,C_PROBE431_TYPE=1,C_PROBE432_TYPE=1,C_PROBE433_TYPE=1,C_PROBE434_TYPE=1,C_PROBE435_TYPE=1,C_PROBE436_TYPE=1,C_PROBE437_TYPE=1,C_PROBE438_TYPE=1,C_PROBE439_TYPE=1,C_PROBE440_TYPE=1,C_PROBE441_TYPE=1,C_PROBE442_TYPE=1,C_PROBE443_TYPE=1,C_PROBE444_TYPE=1,C_PROBE445_TYPE=1,C_PROBE446_TYPE=1,C_PROBE447_TYPE=1,C_PROBE448_TYPE=1,C_PROBE449_TYPE=1,C_PROBE450_TYPE=1,C_PROBE451_TYPE=1,C_PROBE452_TYPE=1,C_PROBE453_TYPE=1,C_PROBE454_TYPE=1,C_PROBE455_TYPE=1,C_PROBE456_TYPE=1,C_PROBE457_TYPE=1,C_PROBE458_TYPE=1,C_PROBE459_TYPE=1,C_PROBE460_TYPE=1,C_PROBE461_TYPE=1,C_PROBE462_TYPE=1,C_PROBE463_TYPE=1,C_PROBE464_TYPE=1,C_PROBE465_TYPE=1,C_PROBE466_TYPE=1,C_PROBE467_TYPE=1,C_PROBE468_TYPE=1,C_PROBE469_TYPE=1,C_PROBE470_TYPE=1,C_PROBE471_TYPE=1,C_PROBE472_TYPE=1,C_PROBE473_TYPE=1,C_PROBE474_TYPE=1,C_PROBE475_TYPE=1,C_PROBE476_TYPE=1,C_PROBE477_TYPE=1,C_PROBE478_TYPE=1,C_PROBE479_TYPE=1,C_PROBE480_TYPE=1,C_PROBE481_TYPE=1,C_PROBE482_TYPE=1,C_PROBE483_TYPE=1,C_PROBE484_TYPE=1,C_PROBE485_TYPE=1,C_PROBE486_TYPE=1,C_PROBE487_TYPE=1,C_PROBE488_TYPE=1,C_PROBE489_TYPE=1,C_PROBE490_TYPE=1,C_PROBE491_TYPE=1,C_PROBE492_TYPE=1,C_PROBE493_TYPE=1,C_PROBE494_TYPE=1,C_PROBE495_TYPE=1,C_PROBE496_TYPE=1,C_PROBE497_TYPE=1,C_PROBE498_TYPE=1,C_PROBE499_TYPE=1,C_PROBE500_TYPE=1,C_PROBE501_TYPE=1,C_PROBE502_TYPE=1,C_PROBE503_TYPE=1,C_PROBE504_TYPE=1,C_PROBE505_TYPE=1,\
C_PROBE506_TYPE=1,C_PROBE507_TYPE=1,C_PROBE508_TYPE=1,C_PROBE509_TYPE=1,C_PROBE510_TYPE=1,C_PROBE511_TYPE=1,C_PROBE512_TYPE=1,C_PROBE513_TYPE=1,C_PROBE514_TYPE=1,C_PROBE515_TYPE=1,C_PROBE516_TYPE=1,C_PROBE517_TYPE=1,C_PROBE518_TYPE=1,C_PROBE519_TYPE=1,C_PROBE520_TYPE=1,C_PROBE521_TYPE=1,C_PROBE522_TYPE=1,C_PROBE523_TYPE=1,C_PROBE524_TYPE=1,C_PROBE525_TYPE=1,C_PROBE526_TYPE=1,C_PROBE527_TYPE=1,C_PROBE528_TYPE=1,C_PROBE529_TYPE=1,C_PROBE530_TYPE=1,C_PROBE531_TYPE=1,C_PROBE532_TYPE=1,C_PROBE533_TYPE=1,C_PROBE534_TYPE=1,C_PROBE535_TYPE=1,C_PROBE536_TYPE=1,C_PROBE537_TYPE=1,C_PROBE538_TYPE=1,C_PROBE539_TYPE=1,C_PROBE540_TYPE=1,C_PROBE541_TYPE=1,C_PROBE542_TYPE=1,C_PROBE543_TYPE=1,C_PROBE544_TYPE=1,C_PROBE545_TYPE=1,C_PROBE546_TYPE=1,C_PROBE547_TYPE=1,C_PROBE548_TYPE=1,C_PROBE549_TYPE=1,C_PROBE550_TYPE=1,C_PROBE551_TYPE=1,C_PROBE552_TYPE=1,C_PROBE553_TYPE=1,C_PROBE554_TYPE=1,C_PROBE555_TYPE=1,C_PROBE556_TYPE=1,C_PROBE557_TYPE=1,C_PROBE558_TYPE=1,C_PROBE559_TYPE=1,C_PROBE560_TYPE=1,C_PROBE561_TYPE=1,C_PROBE562_TYPE=1,C_PROBE563_TYPE=1,C_PROBE564_TYPE=1,C_PROBE565_TYPE=1,C_PROBE566_TYPE=1,C_PROBE567_TYPE=1,C_PROBE568_TYPE=1,C_PROBE569_TYPE=1,C_PROBE570_TYPE=1,C_PROBE571_TYPE=1,C_PROBE572_TYPE=1,C_PROBE573_TYPE=1,C_PROBE574_TYPE=1,C_PROBE575_TYPE=1,C_PROBE576_TYPE=1,C_PROBE577_TYPE=1,C_PROBE578_TYPE=1,C_PROBE579_TYPE=1,C_PROBE580_TYPE=1,C_PROBE581_TYPE=1,C_PROBE582_TYPE=1,C_PROBE583_TYPE=1,C_PROBE584_TYPE=1,C_PROBE585_TYPE=1,C_PROBE586_TYPE=1,C_PROBE587_TYPE=1,C_PROBE588_TYPE=1,C_PROBE589_TYPE=1,C_PROBE590_TYPE=1,C_PROBE591_TYPE=1,C_PROBE592_TYPE=1,C_PROBE593_TYPE=1,C_PROBE594_TYPE=1,C_PROBE595_TYPE=1,C_PROBE596_TYPE=1,C_PROBE597_TYPE=1,C_PROBE598_TYPE=1,C_PROBE599_TYPE=1,C_PROBE600_TYPE=1,C_PROBE601_TYPE=1,C_PROBE602_TYPE=1,C_PROBE603_TYPE=1,C_PROBE604_TYPE=1,C_PROBE605_TYPE=1,\
C_PROBE606_TYPE=1,C_PROBE607_TYPE=1,C_PROBE608_TYPE=1,C_PROBE609_TYPE=1,C_PROBE610_TYPE=1,C_PROBE611_TYPE=1,C_PROBE612_TYPE=1,C_PROBE613_TYPE=1,C_PROBE614_TYPE=1,C_PROBE615_TYPE=1,C_PROBE616_TYPE=1,C_PROBE617_TYPE=1,C_PROBE618_TYPE=1,C_PROBE619_TYPE=1,C_PROBE620_TYPE=1,C_PROBE621_TYPE=1,C_PROBE622_TYPE=1,C_PROBE623_TYPE=1,C_PROBE624_TYPE=1,C_PROBE625_TYPE=1,C_PROBE626_TYPE=1,C_PROBE627_TYPE=1,C_PROBE628_TYPE=1,C_PROBE629_TYPE=1,C_PROBE630_TYPE=1,C_PROBE631_TYPE=1,C_PROBE632_TYPE=1,C_PROBE633_TYPE=1,C_PROBE634_TYPE=1,C_PROBE635_TYPE=1,C_PROBE636_TYPE=1,C_PROBE637_TYPE=1,C_PROBE638_TYPE=1,C_PROBE639_TYPE=1,C_PROBE640_TYPE=1,C_PROBE641_TYPE=1,C_PROBE642_TYPE=1,C_PROBE643_TYPE=1,C_PROBE644_TYPE=1,C_PROBE645_TYPE=1,C_PROBE646_TYPE=1,C_PROBE647_TYPE=1,C_PROBE648_TYPE=1,C_PROBE649_TYPE=1,C_PROBE650_TYPE=1,C_PROBE651_TYPE=1,C_PROBE652_TYPE=1,C_PROBE653_TYPE=1,C_PROBE654_TYPE=1,C_PROBE655_TYPE=1,C_PROBE656_TYPE=1,C_PROBE657_TYPE=1,C_PROBE658_TYPE=1,C_PROBE659_TYPE=1,C_PROBE660_TYPE=1,C_PROBE661_TYPE=1,C_PROBE662_TYPE=1,C_PROBE663_TYPE=1,C_PROBE664_TYPE=1,C_PROBE665_TYPE=1,C_PROBE666_TYPE=1,C_PROBE667_TYPE=1,C_PROBE668_TYPE=1,C_PROBE669_TYPE=1,C_PROBE670_TYPE=1,C_PROBE671_TYPE=1,C_PROBE672_TYPE=1,C_PROBE673_TYPE=1,C_PROBE674_TYPE=1,C_PROBE675_TYPE=1,C_PROBE676_TYPE=1,C_PROBE677_TYPE=1,C_PROBE678_TYPE=1,C_PROBE679_TYPE=1,C_PROBE680_TYPE=1,C_PROBE681_TYPE=1,C_PROBE682_TYPE=1,C_PROBE683_TYPE=1,C_PROBE684_TYPE=1,C_PROBE685_TYPE=1,C_PROBE686_TYPE=1,C_PROBE687_TYPE=1,C_PROBE688_TYPE=1,C_PROBE689_TYPE=1,C_PROBE690_TYPE=1,C_PROBE691_TYPE=1,C_PROBE692_TYPE=1,C_PROBE693_TYPE=1,C_PROBE694_TYPE=1,C_PROBE695_TYPE=1,C_PROBE696_TYPE=1,C_PROBE697_TYPE=1,C_PROBE698_TYPE=1,C_PROBE699_TYPE=1,C_PROBE700_TYPE=1,C_PROBE701_TYPE=1,C_PROBE702_TYPE=1,C_PROBE703_TYPE=1,C_PROBE704_TYPE=1,C_PROBE705_TYPE=1,\
C_PROBE706_TYPE=1,C_PROBE707_TYPE=1,C_PROBE708_TYPE=1,C_PROBE709_TYPE=1,C_PROBE710_TYPE=1,C_PROBE711_TYPE=1,C_PROBE712_TYPE=1,C_PROBE713_TYPE=1,C_PROBE714_TYPE=1,C_PROBE715_TYPE=1,C_PROBE716_TYPE=1,C_PROBE717_TYPE=1,C_PROBE718_TYPE=1,C_PROBE719_TYPE=1,C_PROBE720_TYPE=1,C_PROBE721_TYPE=1,C_PROBE722_TYPE=1,C_PROBE723_TYPE=1,C_PROBE724_TYPE=1,C_PROBE725_TYPE=1,C_PROBE726_TYPE=1,C_PROBE727_TYPE=1,C_PROBE728_TYPE=1,C_PROBE729_TYPE=1,C_PROBE730_TYPE=1,C_PROBE731_TYPE=1,C_PROBE732_TYPE=1,C_PROBE733_TYPE=1,C_PROBE734_TYPE=1,C_PROBE735_TYPE=1,C_PROBE736_TYPE=1,C_PROBE737_TYPE=1,C_PROBE738_TYPE=1,C_PROBE739_TYPE=1,C_PROBE740_TYPE=1,C_PROBE741_TYPE=1,C_PROBE742_TYPE=1,C_PROBE743_TYPE=1,C_PROBE744_TYPE=1,C_PROBE745_TYPE=1,C_PROBE746_TYPE=1,C_PROBE747_TYPE=1,C_PROBE748_TYPE=1,C_PROBE749_TYPE=1,C_PROBE750_TYPE=1,C_PROBE751_TYPE=1,C_PROBE752_TYPE=1,C_PROBE753_TYPE=1,C_PROBE754_TYPE=1,C_PROBE755_TYPE=1,C_PROBE756_TYPE=1,C_PROBE757_TYPE=1,C_PROBE758_TYPE=1,C_PROBE759_TYPE=1,C_PROBE760_TYPE=1,C_PROBE761_TYPE=1,C_PROBE762_TYPE=1,C_PROBE763_TYPE=1,C_PROBE764_TYPE=1,C_PROBE765_TYPE=1,C_PROBE766_TYPE=1,C_PROBE767_TYPE=1,C_PROBE768_TYPE=1,C_PROBE769_TYPE=1,C_PROBE770_TYPE=1,C_PROBE771_TYPE=1,C_PROBE772_TYPE=1,C_PROBE773_TYPE=1,C_PROBE774_TYPE=1,C_PROBE775_TYPE=1,C_PROBE776_TYPE=1,C_PROBE777_TYPE=1,C_PROBE778_TYPE=1,C_PROBE779_TYPE=1,C_PROBE780_TYPE=1,C_PROBE781_TYPE=1,C_PROBE782_TYPE=1,C_PROBE783_TYPE=1,C_PROBE784_TYPE=1,C_PROBE785_TYPE=1,C_PROBE786_TYPE=1,C_PROBE787_TYPE=1,C_PROBE788_TYPE=1,C_PROBE789_TYPE=1,C_PROBE790_TYPE=1,C_PROBE791_TYPE=1,C_PROBE792_TYPE=1,C_PROBE793_TYPE=1,C_PROBE794_TYPE=1,C_PROBE795_TYPE=1,C_PROBE796_TYPE=1,C_PROBE797_TYPE=1,C_PROBE798_TYPE=1,C_PROBE799_TYPE=1,C_PROBE800_TYPE=1,C_PROBE801_TYPE=1,C_PROBE802_TYPE=1,C_PROBE803_TYPE=1,C_PROBE804_TYPE=1,C_PROBE805_TYPE=1,\
C_PROBE806_TYPE=1,C_PROBE807_TYPE=1,C_PROBE808_TYPE=1,C_PROBE809_TYPE=1,C_PROBE810_TYPE=1,C_PROBE811_TYPE=1,C_PROBE812_TYPE=1,C_PROBE813_TYPE=1,C_PROBE814_TYPE=1,C_PROBE815_TYPE=1,C_PROBE816_TYPE=1,C_PROBE817_TYPE=1,C_PROBE818_TYPE=1,C_PROBE819_TYPE=1,C_PROBE820_TYPE=1,C_PROBE821_TYPE=1,C_PROBE822_TYPE=1,C_PROBE823_TYPE=1,C_PROBE824_TYPE=1,C_PROBE825_TYPE=1,C_PROBE826_TYPE=1,C_PROBE827_TYPE=1,C_PROBE828_TYPE=1,C_PROBE829_TYPE=1,C_PROBE830_TYPE=1,C_PROBE831_TYPE=1,C_PROBE832_TYPE=1,C_PROBE833_TYPE=1,C_PROBE834_TYPE=1,C_PROBE835_TYPE=1,C_PROBE836_TYPE=1,C_PROBE837_TYPE=1,C_PROBE838_TYPE=1,C_PROBE839_TYPE=1,C_PROBE840_TYPE=1,C_PROBE841_TYPE=1,C_PROBE842_TYPE=1,C_PROBE843_TYPE=1,C_PROBE844_TYPE=1,C_PROBE845_TYPE=1,C_PROBE846_TYPE=1,C_PROBE847_TYPE=1,C_PROBE848_TYPE=1,C_PROBE849_TYPE=1,C_PROBE850_TYPE=1,C_PROBE851_TYPE=1,C_PROBE852_TYPE=1,C_PROBE853_TYPE=1,C_PROBE854_TYPE=1,C_PROBE855_TYPE=1,C_PROBE856_TYPE=1,C_PROBE857_TYPE=1,C_PROBE858_TYPE=1,C_PROBE859_TYPE=1,C_PROBE860_TYPE=1,C_PROBE861_TYPE=1,C_PROBE862_TYPE=1,C_PROBE863_TYPE=1,C_PROBE864_TYPE=1,C_PROBE865_TYPE=1,C_PROBE866_TYPE=1,C_PROBE867_TYPE=1,C_PROBE868_TYPE=1,C_PROBE869_TYPE=1,C_PROBE870_TYPE=1,C_PROBE871_TYPE=1,C_PROBE872_TYPE=1,C_PROBE873_TYPE=1,C_PROBE874_TYPE=1,C_PROBE875_TYPE=1,C_PROBE876_TYPE=1,C_PROBE877_TYPE=1,C_PROBE878_TYPE=1,C_PROBE879_TYPE=1,C_PROBE880_TYPE=1,C_PROBE881_TYPE=1,C_PROBE882_TYPE=1,C_PROBE883_TYPE=1,C_PROBE884_TYPE=1,C_PROBE885_TYPE=1,C_PROBE886_TYPE=1,C_PROBE887_TYPE=1,C_PROBE888_TYPE=1,C_PROBE889_TYPE=1,C_PROBE890_TYPE=1,C_PROBE891_TYPE=1,C_PROBE892_TYPE=1,C_PROBE893_TYPE=1,C_PROBE894_TYPE=1,C_PROBE895_TYPE=1,C_PROBE896_TYPE=1,C_PROBE897_TYPE=1,C_PROBE898_TYPE=1,C_PROBE899_TYPE=1,C_PROBE900_TYPE=1,C_PROBE901_TYPE=1,C_PROBE902_TYPE=1,C_PROBE903_TYPE=1,C_PROBE904_TYPE=1,C_PROBE905_TYPE=1,\
C_PROBE906_TYPE=1,C_PROBE907_TYPE=1,C_PROBE908_TYPE=1,C_PROBE909_TYPE=1,C_PROBE910_TYPE=1,C_PROBE911_TYPE=1,C_PROBE912_TYPE=1,C_PROBE913_TYPE=1,C_PROBE914_TYPE=1,C_PROBE915_TYPE=1,C_PROBE916_TYPE=1,C_PROBE917_TYPE=1,C_PROBE918_TYPE=1,C_PROBE919_TYPE=1,C_PROBE920_TYPE=1,C_PROBE921_TYPE=1,C_PROBE922_TYPE=1,C_PROBE923_TYPE=1,C_PROBE924_TYPE=1,C_PROBE925_TYPE=1,C_PROBE926_TYPE=1,C_PROBE927_TYPE=1,C_PROBE928_TYPE=1,C_PROBE929_TYPE=1,C_PROBE930_TYPE=1,C_PROBE931_TYPE=1,C_PROBE932_TYPE=1,C_PROBE933_TYPE=1,C_PROBE934_TYPE=1,C_PROBE935_TYPE=1,C_PROBE936_TYPE=1,C_PROBE937_TYPE=1,C_PROBE938_TYPE=1,C_PROBE939_TYPE=1,C_PROBE940_TYPE=1,C_PROBE941_TYPE=1,C_PROBE942_TYPE=1,C_PROBE943_TYPE=1,C_PROBE944_TYPE=1,C_PROBE945_TYPE=1,C_PROBE946_TYPE=1,C_PROBE947_TYPE=1,C_PROBE948_TYPE=1,C_PROBE949_TYPE=1,C_PROBE950_TYPE=1,C_PROBE951_TYPE=1,C_PROBE952_TYPE=1,C_PROBE953_TYPE=1,C_PROBE954_TYPE=1,C_PROBE955_TYPE=1,C_PROBE956_TYPE=1,C_PROBE957_TYPE=1,C_PROBE958_TYPE=1,C_PROBE959_TYPE=1,C_PROBE960_TYPE=1,C_PROBE961_TYPE=1,C_PROBE962_TYPE=1,C_PROBE963_TYPE=1,C_PROBE964_TYPE=1,C_PROBE965_TYPE=1,C_PROBE966_TYPE=1,C_PROBE967_TYPE=1,C_PROBE968_TYPE=1,C_PROBE969_TYPE=1,C_PROBE970_TYPE=1,C_PROBE971_TYPE=1,C_PROBE972_TYPE=1,C_PROBE973_TYPE=1,C_PROBE974_TYPE=1,C_PROBE975_TYPE=1,C_PROBE976_TYPE=1,C_PROBE977_TYPE=1,C_PROBE978_TYPE=1,C_PROBE979_TYPE=1,C_PROBE980_TYPE=1,C_PROBE981_TYPE=1,C_PROBE982_TYPE=1,C_PROBE983_TYPE=1,C_PROBE984_TYPE=1,C_PROBE985_TYPE=1,C_PROBE986_TYPE=1,C_PROBE987_TYPE=1,C_PROBE988_TYPE=1,C_PROBE989_TYPE=1,C_PROBE990_TYPE=1,C_PROBE991_TYPE=1,C_PROBE992_TYPE=1,C_PROBE993_TYPE=1,C_PROBE994_TYPE=1,C_PROBE995_TYPE=1,C_PROBE996_TYPE=1,C_PROBE997_TYPE=1,C_PROBE998_TYPE=1,C_PROBE999_TYPE=1,C_PROBE1000_TYPE=1,C_PROBE1001_TYPE=1,C_PROBE1002_TYPE=1,C_PROBE1003_TYPE=1,C_PROBE1004_TYPE=1,C_PROBE1005_TYPE=1,\
C_PROBE1006_TYPE=1,C_PROBE1007_TYPE=1,C_PROBE1008_TYPE=1,C_PROBE1009_TYPE=1,C_PROBE1010_TYPE=1,C_PROBE1011_TYPE=1,C_PROBE1012_TYPE=1,C_PROBE1013_TYPE=1,C_PROBE1014_TYPE=1,C_PROBE1015_TYPE=1,C_PROBE1016_TYPE=1,C_PROBE1017_TYPE=1,C_PROBE1018_TYPE=1,C_PROBE1019_TYPE=1,C_PROBE1020_TYPE=1,C_PROBE1021_TYPE=1,C_PROBE1022_TYPE=1,C_PROBE1023_TYPE=1}" *)

module ila_0 (
clk,


probe0,
probe1,
probe2,
probe3,
probe4,
probe5,
probe6,
probe7,
probe8,
probe9,
probe10,
probe11,
probe12,
probe13,
probe14,
probe15,
probe16,
probe17,
probe18,
probe19,
probe20,
probe21,
probe22,
probe23,
probe24,
probe25,
probe26,
probe27
);

input clk;


input [24 : 0] probe0;
input [23 : 0] probe1;
input [7 : 0] probe2;
input [0 : 0] probe3;
input [0 : 0] probe4;
input [3 : 0] probe5;
input [24 : 0] probe6;
input [0 : 0] probe7;
input [0 : 0] probe8;
input [7 : 0] probe9;
input [15 : 0] probe10;
input [0 : 0] probe11;
input [0 : 0] probe12;
input [3 : 0] probe13;
input [7 : 0] probe14;
input [0 : 0] probe15;
input [0 : 0] probe16;
input [0 : 0] probe17;
input [0 : 0] probe18;
input [0 : 0] probe19;
input [0 : 0] probe20;
input [0 : 0] probe21;
input [0 : 0] probe22;
input [0 : 0] probe23;
input [15 : 0] probe24;
input [7 : 0] probe25;
input [0 : 0] probe26;
input [0 : 0] probe27;


wire [16:0] sl_oport0;
wire [36:0] sl_iport0;
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
