jabadiagm/MSXgoauld_x/fpga/Goauld_x.srcs/sources_1/ip/clk_wiz_0_1/clk_wiz_0_stub.v

// Copyright 1986-2019 Xilinx, Inc. All Rights Reserved.
// --------------------------------------------------------------------------------
// Tool Version: Vivado v.2019.1 (win64) Build 2552052 Fri May 24 14:49:42 MDT 2019
// Date        : Fri Jun 21 11:57:39 2024
// Host        : DELL running 64-bit major release  (build 9200)
// Command     : write_verilog -force -mode synth_stub
//               D:/datos/proyectos/45_QMTECH_XC7A15T/21_Goauld_x_oficial/Goauld_x.srcs/sources_1/ip/clk_wiz_0_1/clk_wiz_0_stub.v
// Design      : clk_wiz_0
// Purpose     : Stub declaration of top-level module interface
// Device      : xc7a35tcsg325-1
// --------------------------------------------------------------------------------

// This empty module with port declaration file causes synthesis tools to infer a black box for IP.
// The synthesis directives are for Synopsys Synplify support to prevent IO buffer insertion.
// Please paste the declaration into a Verilog source file or add the file as an additional source.
module clk_wiz_0(clk_out1, clk_out2, clk_out3, clk_out4, clk_in1)
/* synthesis syn_black_box black_box_pad_pin="clk_out1,clk_out2,clk_out3,clk_out4,clk_in1" */;
  output clk_out1;
  output clk_out2;
  output clk_out3;
  output clk_out4;
  input clk_in1;
endmodule
