jabadiagm/MSXgoauld_x/fpga/Goauld_x.srcs/sources_1/ip/clk_wiz_0_1/clk_wiz_0_stub.vhdl

-- Copyright 1986-2019 Xilinx, Inc. All Rights Reserved.
-- --------------------------------------------------------------------------------
-- Tool Version: Vivado v.2019.1 (win64) Build 2552052 Fri May 24 14:49:42 MDT 2019
-- Date        : Fri Jun 21 11:57:39 2024
-- Host        : DELL running 64-bit major release  (build 9200)
-- Command     : write_vhdl -force -mode synth_stub
--               D:/datos/proyectos/45_QMTECH_XC7A15T/21_Goauld_x_oficial/Goauld_x.srcs/sources_1/ip/clk_wiz_0_1/clk_wiz_0_stub.vhdl
-- Design      : clk_wiz_0
-- Purpose     : Stub declaration of top-level module interface
-- Device      : xc7a35tcsg325-1
-- --------------------------------------------------------------------------------
library IEEE;
use IEEE.STD_LOGIC_1164.ALL;

entity clk_wiz_0 is
  Port ( 
    clk_out1 : out STD_LOGIC;
    clk_out2 : out STD_LOGIC;
    clk_out3 : out STD_LOGIC;
    clk_out4 : out STD_LOGIC;
    clk_in1 : in STD_LOGIC
  );

end clk_wiz_0;

architecture stub of clk_wiz_0 is
attribute syn_black_box : boolean;
attribute black_box_pad_pin : string;
attribute syn_black_box of stub : architecture is true;
attribute black_box_pad_pin of stub : architecture is "clk_out1,clk_out2,clk_out3,clk_out4,clk_in1";
begin
end;
