jabadiagm/MSXgoauld_x/fpga/Goauld_x.srcs/sources_1/ip/ila_0_1/ila_0_stub.vhdl

-- Copyright 1986-2019 Xilinx, Inc. All Rights Reserved.
-- --------------------------------------------------------------------------------
-- Tool Version: Vivado v.2019.1 (win64) Build 2552052 Fri May 24 14:49:42 MDT 2019
-- Date        : Tue May 21 19:43:43 2024
-- Host        : DELL running 64-bit major release  (build 9200)
-- Command     : write_vhdl -force -mode synth_stub -rename_top ila_0 -prefix
--               ila_0_ ila_0_stub.vhdl
-- Design      : ila_0
-- Purpose     : Stub declaration of top-level module interface
-- Device      : xc7a35tcsg325-1
-- --------------------------------------------------------------------------------
library IEEE;
use IEEE.STD_LOGIC_1164.ALL;

entity ila_0 is
  Port ( 
    clk : in STD_LOGIC;
    probe0 : in STD_LOGIC_VECTOR ( 24 downto 0 );
    probe1 : in STD_LOGIC_VECTOR ( 23 downto 0 );
    probe2 : in STD_LOGIC_VECTOR ( 7 downto 0 );
    probe3 : in STD_LOGIC_VECTOR ( 0 to 0 );
    probe4 : in STD_LOGIC_VECTOR ( 0 to 0 );
    probe5 : in STD_LOGIC_VECTOR ( 3 downto 0 );
    probe6 : in STD_LOGIC_VECTOR ( 24 downto 0 );
    probe7 : in STD_LOGIC_VECTOR ( 0 to 0 );
    probe8 : in STD_LOGIC_VECTOR ( 0 to 0 );
    probe9 : in STD_LOGIC_VECTOR ( 7 downto 0 );
    probe10 : in STD_LOGIC_VECTOR ( 15 downto 0 );
    probe11 : in STD_LOGIC_VECTOR ( 0 to 0 );
    probe12 : in STD_LOGIC_VECTOR ( 0 to 0 );
    probe13 : in STD_LOGIC_VECTOR ( 3 downto 0 );
    probe14 : in STD_LOGIC_VECTOR ( 7 downto 0 );
    probe15 : in STD_LOGIC_VECTOR ( 0 to 0 );
    probe16 : in STD_LOGIC_VECTOR ( 0 to 0 );
    probe17 : in STD_LOGIC_VECTOR ( 0 to 0 );
    probe18 : in STD_LOGIC_VECTOR ( 0 to 0 );
    probe19 : in STD_LOGIC_VECTOR ( 0 to 0 );
    probe20 : in STD_LOGIC_VECTOR ( 0 to 0 );
    probe21 : in STD_LOGIC_VECTOR ( 0 to 0 );
    probe22 : in STD_LOGIC_VECTOR ( 0 to 0 );
    probe23 : in STD_LOGIC_VECTOR ( 0 to 0 );
    probe24 : in STD_LOGIC_VECTOR ( 15 downto 0 );
    probe25 : in STD_LOGIC_VECTOR ( 7 downto 0 );
    probe26 : in STD_LOGIC_VECTOR ( 0 to 0 );
    probe27 : in STD_LOGIC_VECTOR ( 0 to 0 )
  );

end ila_0;

architecture stub of ila_0 is
attribute syn_black_box : boolean;
attribute black_box_pad_pin : string;
attribute syn_black_box of stub : architecture is true;
attribute black_box_pad_pin of stub : architecture is "clk,probe0[24:0],probe1[23:0],probe2[7:0],probe3[0:0],probe4[0:0],probe5[3:0],probe6[24:0],probe7[0:0],probe8[0:0],probe9[7:0],probe10[15:0],probe11[0:0],probe12[0:0],probe13[3:0],probe14[7:0],probe15[0:0],probe16[0:0],probe17[0:0],probe18[0:0],probe19[0:0],probe20[0:0],probe21[0:0],probe22[0:0],probe23[0:0],probe24[15:0],probe25[7:0],probe26[0:0],probe27[0:0]";
attribute X_CORE_INFO : string;
attribute X_CORE_INFO of stub : architecture is "ila,Vivado 2019.1";
begin
end;
